sastles-com/FPC-isolation-sphere/blog/tips/ai-conversational-design.md

---
title: "AIと対話しながらハードを設計する —— Claude Codeで球体LEDを作る"
emoji: "🤖"
type: "idea"
topics: ["AI", "ClaudeCode", "設計", "ものづくり", "電子工作"]
published: false
---

> **アウトライン（note=物語 / Zenn idea=両出し）** — 本編リンク元: 00 序章（メタ視点）
> プロセスもの。技術詳細より「どう進めたか」の体験談。最も拡散しうる一本。

## なぜAI対話で設計したのか
- 球体LEDという**幾何 × 回路 × 機構 × ソフト**の横断プロジェクト
- 一人で全領域を抱えるより、AIを設計パートナーにする実験

## ワークフローの実際
- リポジトリに設計知識を集約（`CLAUDE.md` + `docs/NN-*.md`）→ AIが前提を常に把握
- 「確定事項」と「未確定（open questions）」を分けて管理 → AIが勝手に決めない
- スクリプト生成（Goldberg多面体、FPC展開、LED座標CSV）を対話で回す

## うまくいったこと
- 幾何の対称性（5回対称→Gerber1種×10）など、**設計判断の言語化**が進んだ
- ドキュメントが常に最新 → 数ヶ月後の自分が即復帰できる
- 「なぜこの設計か」が対話ログとして残る

## 難しかった・気をつけたこと
- AIが推論で埋めようとする → **「不明点は質問させる」ルール**を明文化
- 確定/未確定の境界管理、ハード規則（NEVER/ALWAYS）の固定
- 最終判断は人間（特に試作検証が要る物理パラメータ）

## この記事自体もAIと書いている
- ブログの章立て・媒体戦略もAIと壁打ちした、というメタなオチ

## 関連
- 本編: 00 序章 / 全シリーズの裏側
