sastles-com/FPC-isolation-sphere/blog/tips/shell-color-black-or-white.md

---
title: "外殻は白か黒か？ —— 球体LEDディスプレイの外装色を決める"
emoji: "⚫"
type: "tech"
topics: ["3Dプリンタ", "電子工作", "LED", "設計", "光学"]
published: false
---

> **アウトライン（Zenn Scrap向き：結論が固まったらArticle化）** — 本編リンク元: 01 シェル設計
> 設計docsの方針: 黒（反射抑制のブラックマスク効果）。本記事はそのトレードオフを言語化する。

## 何を悩んでいるか
- 外装色は見た目だけでなく**光学性能**を左右する設計パラメータ
- 候補: 黒 / 白 / その他（グレー・スモーク等）

## 黒のメリット
- ラッパ穴周囲が**遮光マスク**になり、隣接LEDの光の滲みを抑え**コントラスト向上**
- 消灯時に「黒い球」として締まる、映像の黒が沈む
- 反射抑制 → 球面の映像が読みやすい

## 白のメリット（と却下理由）
- 拡散して柔らかい印象 / 消灯時の存在感
- ただし**滲み・コントラスト低下** → 映像ディスプレイとしては不利

## ラッパ穴構造との相互作用
- 黒 + 円錐ラッパ穴 = 二重のブラックマスク（記事01と接続）
- PETG黒の表面処理（マット/グロス）で反射がどう変わるか

## 決定と根拠
- **黒を採用**（ディスプレイとしてのコントラスト最優先）
- 試作で詰める点: マット/グロス、艶消し塗装の要否、内面反射の実測

## 関連
- 本編: 01 シェル設計（ラッパ穴の光学設計）
