sastles-com/FPC-isolation-sphere/docs/各図.pptx

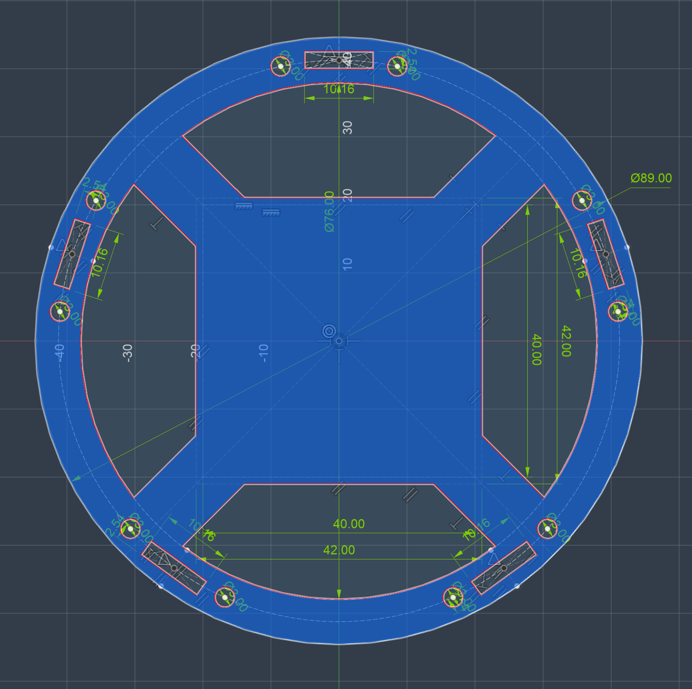
[picture p6: figure]

マザーリング

ポゴピン

電池・基板スペース

## Slide 2

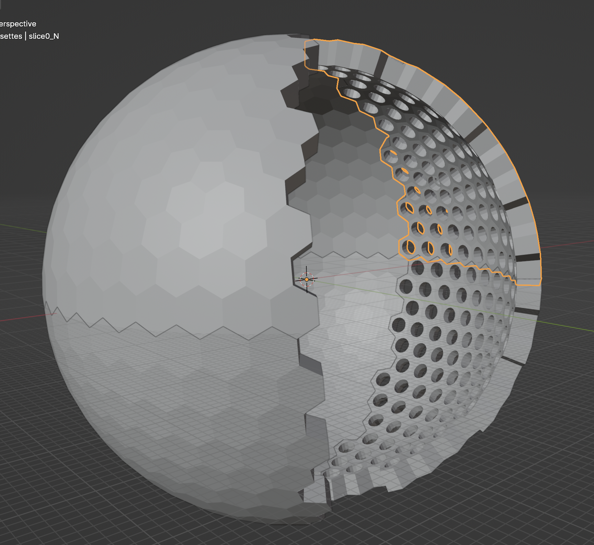
[picture p7: figure]

## Slide 3
