sastles-com/FPC-isolation-sphere/blog/images/28dac7f0-c07c-42df-aeb3-657aa2e844b5.jpeg

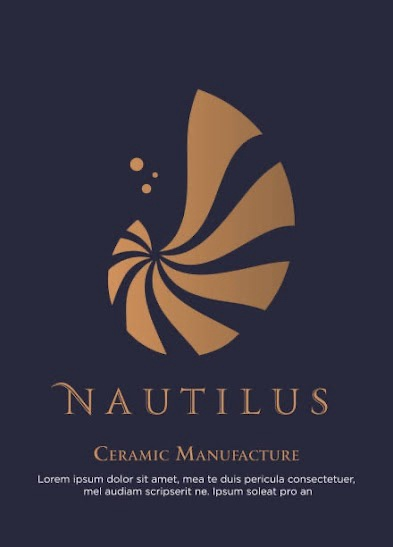
blog/images/28dac7f0-c07c-42df-aeb3-657aa2e844b5.jpeg
