sastles-com/FPC-isolation-sphere/blog/images/2025/IMG_6954.PNG

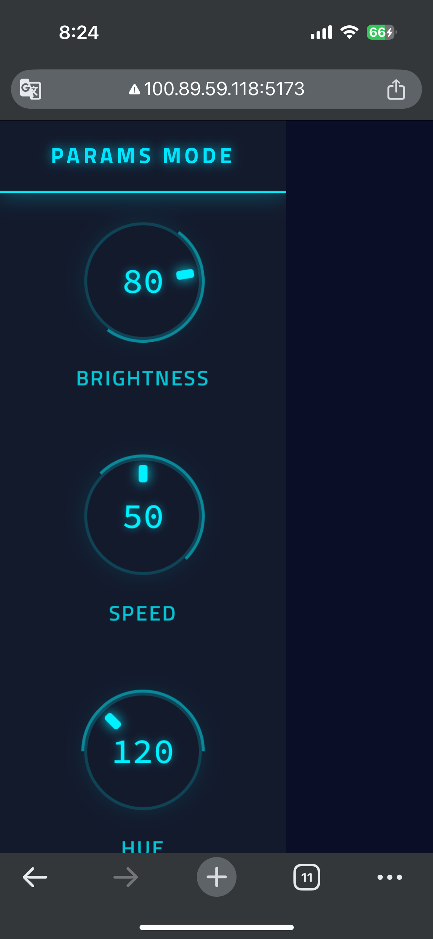
blog/images/2025/IMG_6954.PNG
