sastles-com/FPC-isolation-sphere/blog/images/2025/IMG_6956.PNG

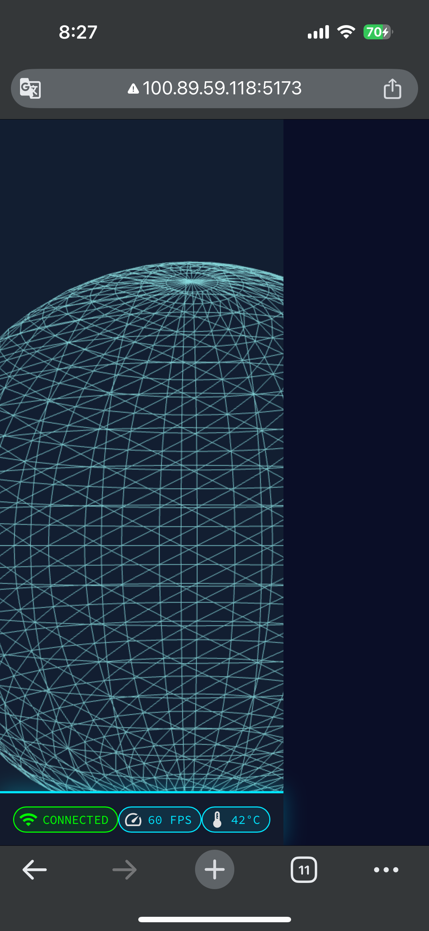
blog/images/2025/IMG_6956.PNG
