sastles-com/FPC-isolation-sphere/blog/images/2025/IMG_7172.PNG

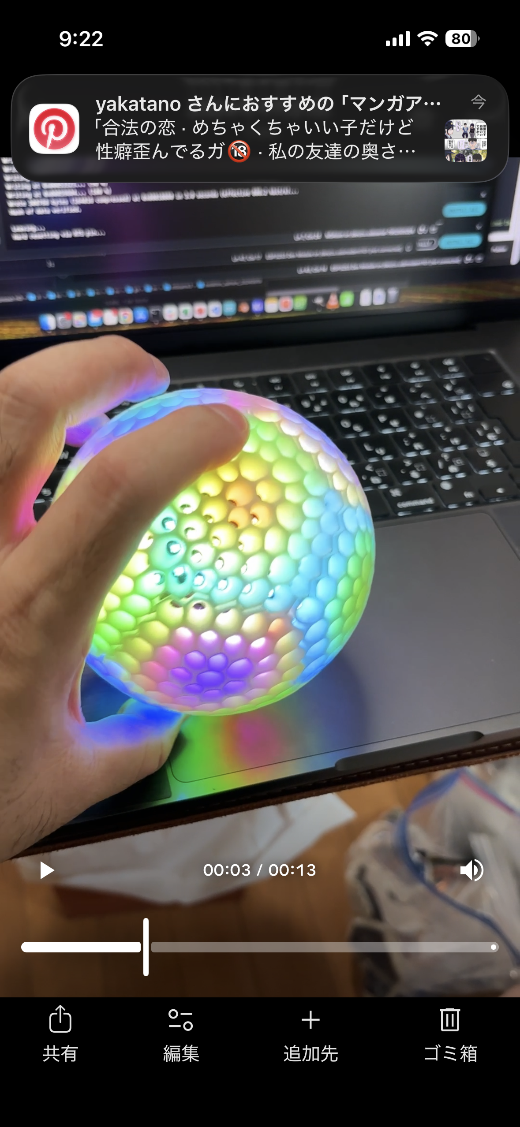
blog/images/2025/IMG_7172.PNG
