sastles-com/FPC-isolation-sphere/blog/images/2025/IMG_7173.PNG

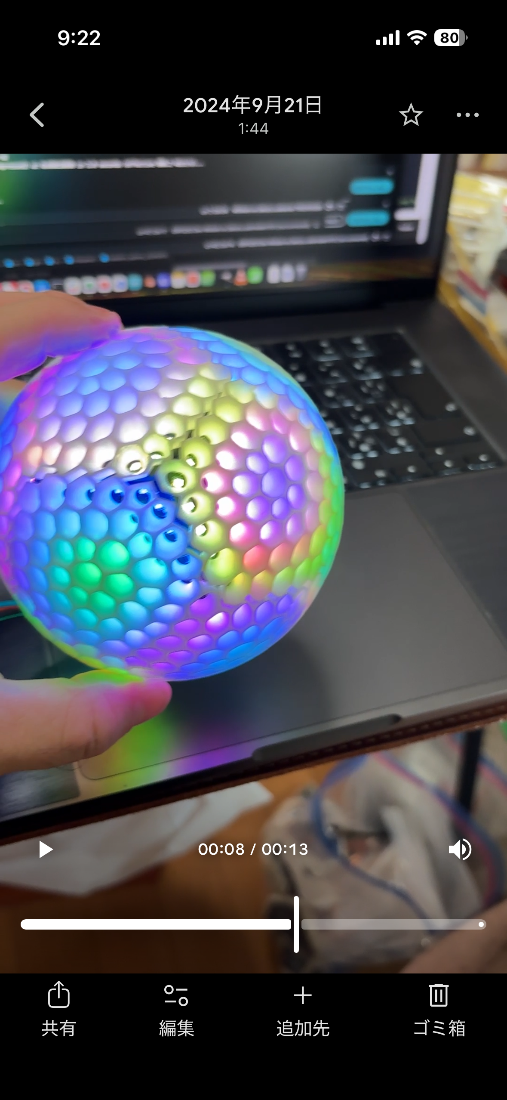
blog/images/2025/IMG_7173.PNG
