sastles-com/FPC-isolation-sphere/blog/images/avocado/IMG_8150.JPG

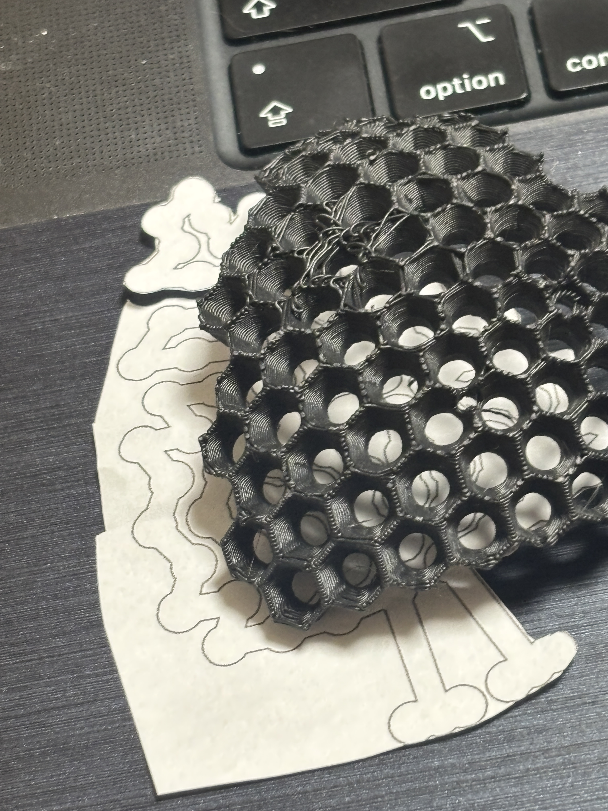
blog/images/avocado/IMG_8150.JPG
