sastles-com/FPC-isolation-sphere/blog/images/avocado/IMG_8152.JPG

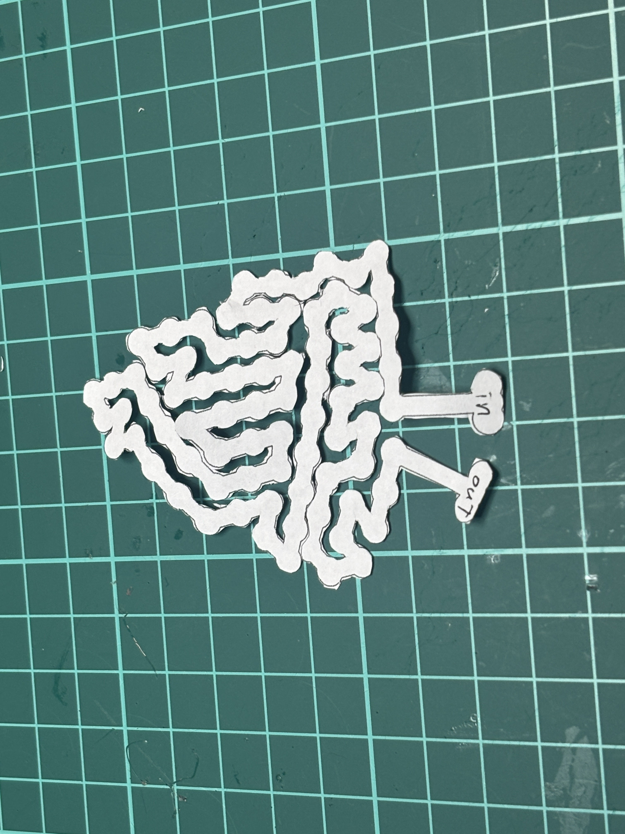
blog/images/avocado/IMG_8152.JPG
