sastles-com/FPC-isolation-sphere/blog/images/avocado/IMG_8159.JPG

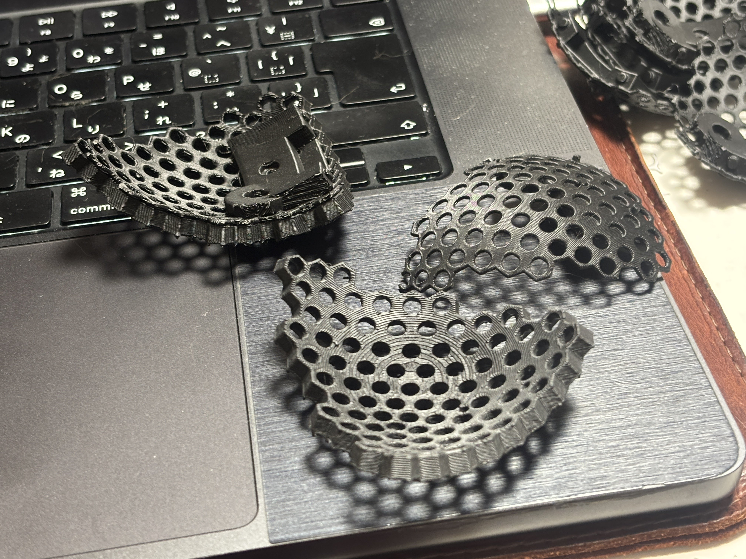
blog/images/avocado/IMG_8159.JPG
