sastles-com/FPC-isolation-sphere/blog/images/avocado/IMG_8160.JPG

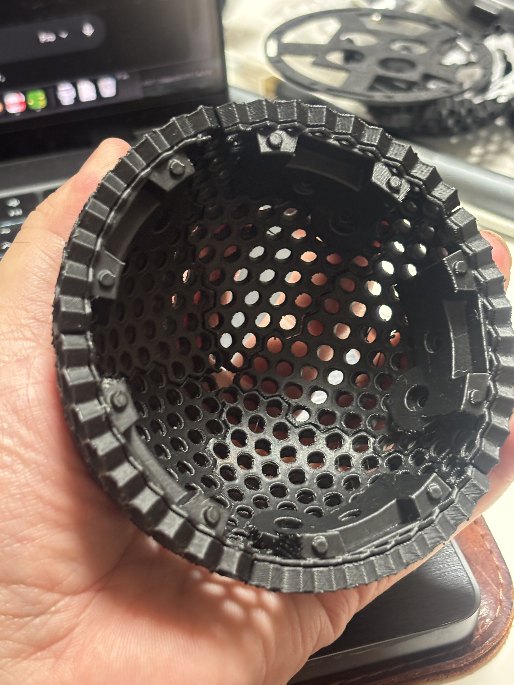
blog/images/avocado/IMG_8160.JPG
