sastles-com/FPC-isolation-sphere/blog/images/avocado/IMG_8166.JPG

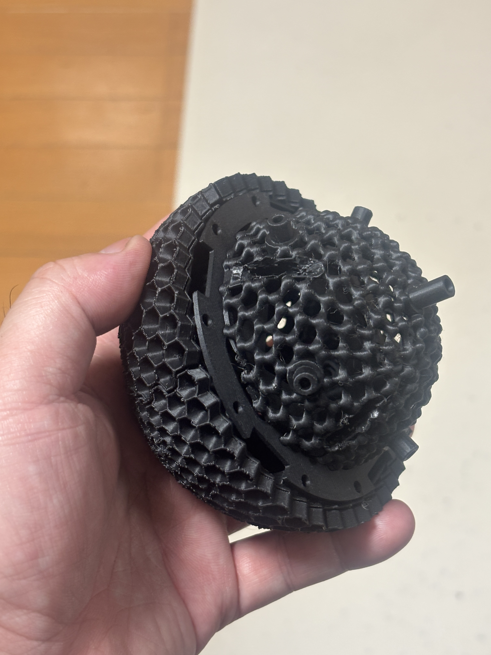
blog/images/avocado/IMG_8166.JPG
