sastles-com/FPC-isolation-sphere/blog/images/avocado/IMG_8167.JPG

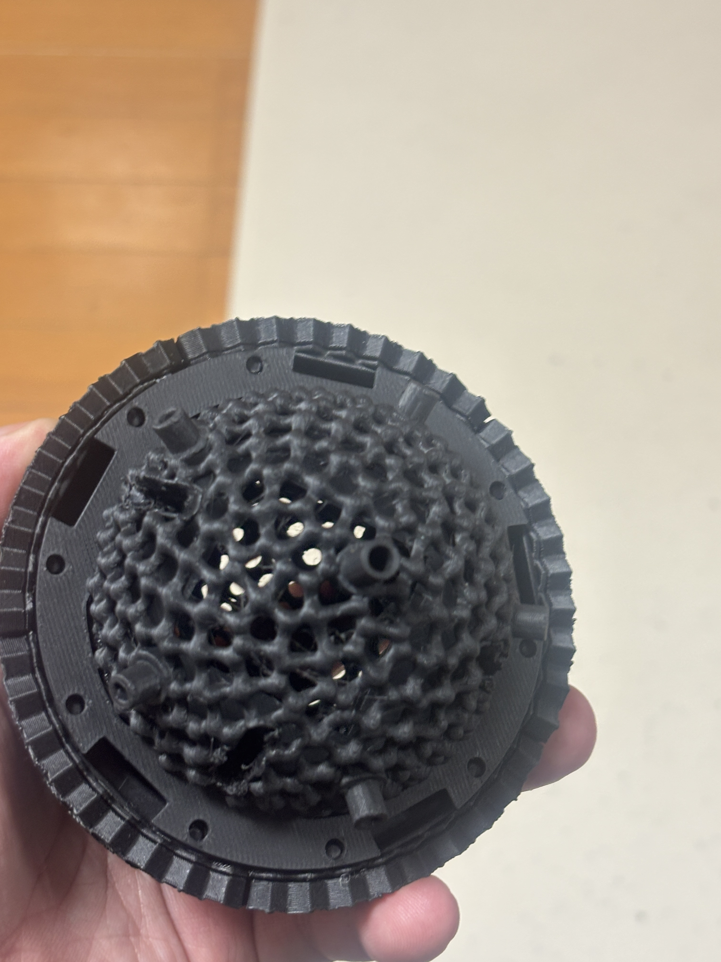
blog/images/avocado/IMG_8167.JPG
