sastles-com/FPC-isolation-sphere/blog/images/avocado/IMG_8190.JPG

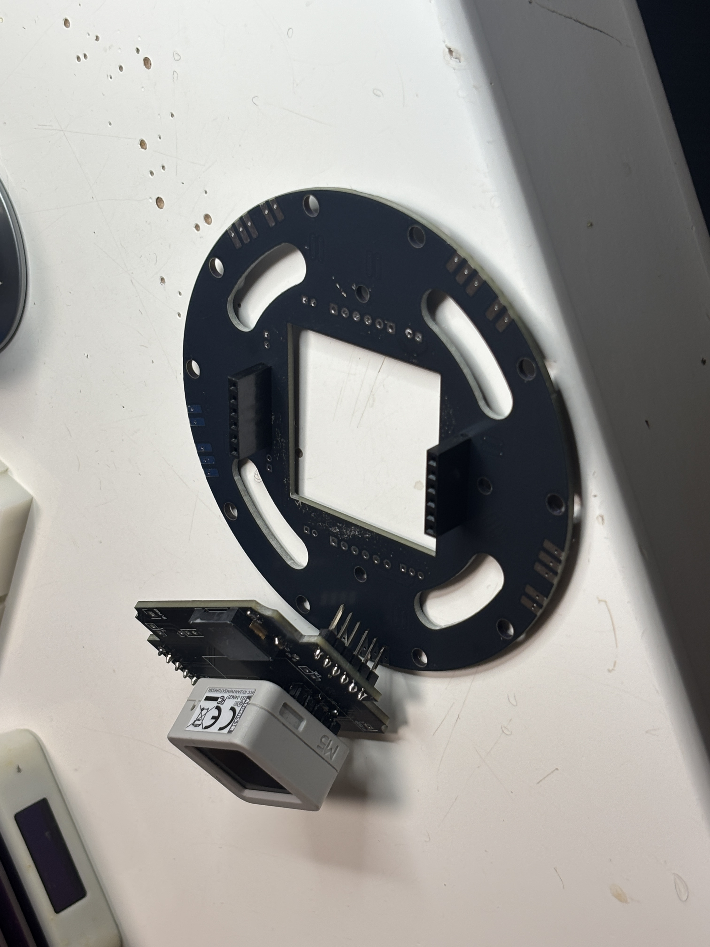
blog/images/avocado/IMG_8190.JPG
