sastles-com/FPC-isolation-sphere/blog/images/avocado/IMG_8191.JPG

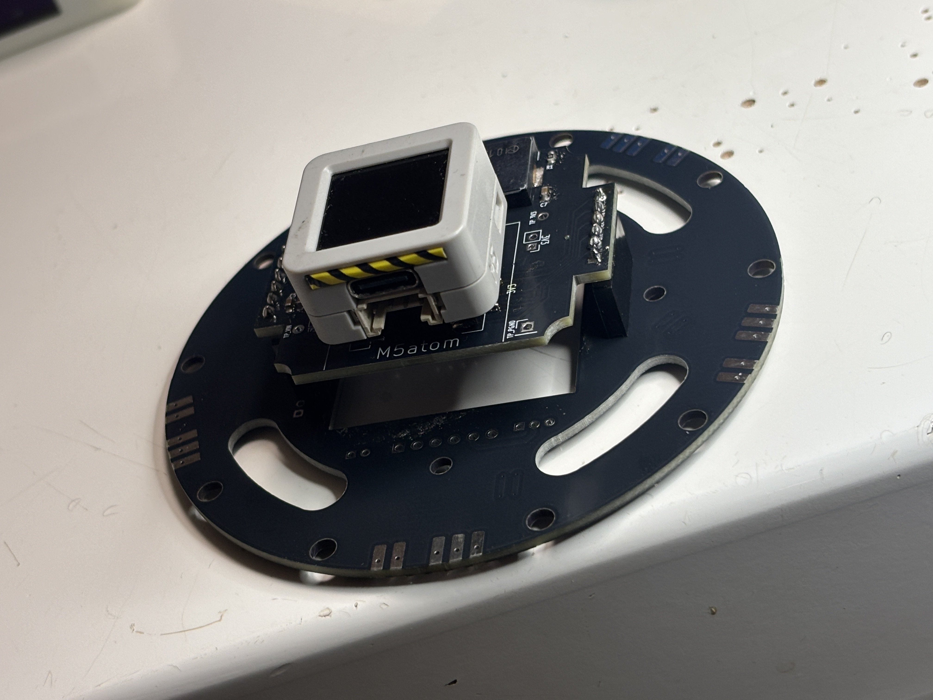
blog/images/avocado/IMG_8191.JPG
