sastles-com/FPC-isolation-sphere/blog/images/avocado/IMG_8192.JPG

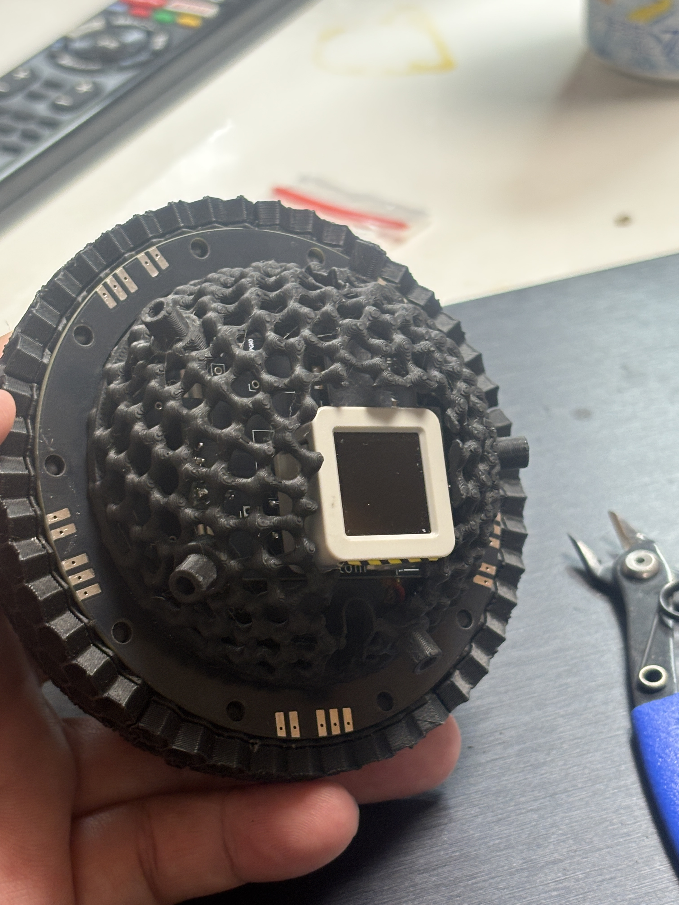
blog/images/avocado/IMG_8192.JPG
