sastles-com/FPC-isolation-sphere/blog/images/avocado/IMG_8193.JPG

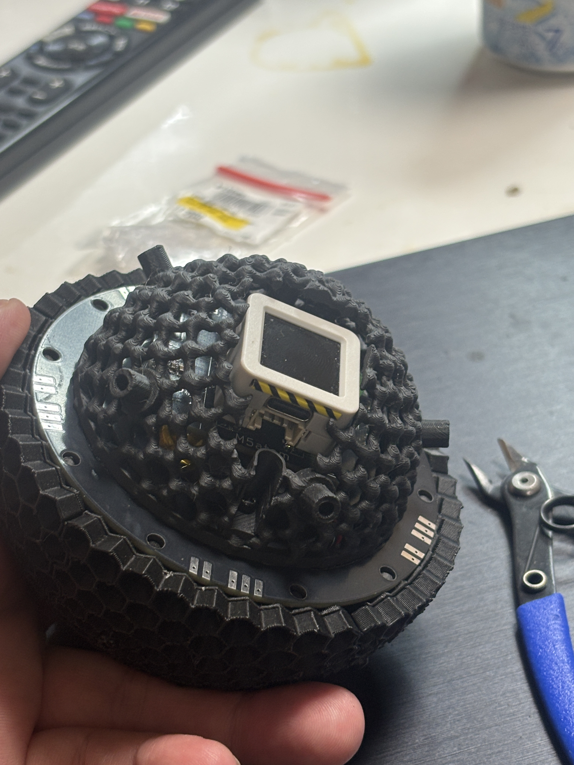
blog/images/avocado/IMG_8193.JPG
