sastles-com/FPC-isolation-sphere/blog/images/avocado/IMG_8194.JPG

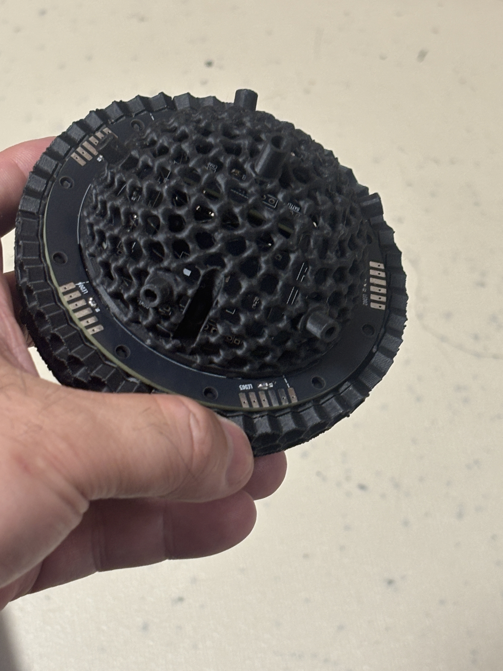
blog/images/avocado/IMG_8194.JPG
