sastles-com/FPC-isolation-sphere/blog/images/avocado/IMG_8195.JPG

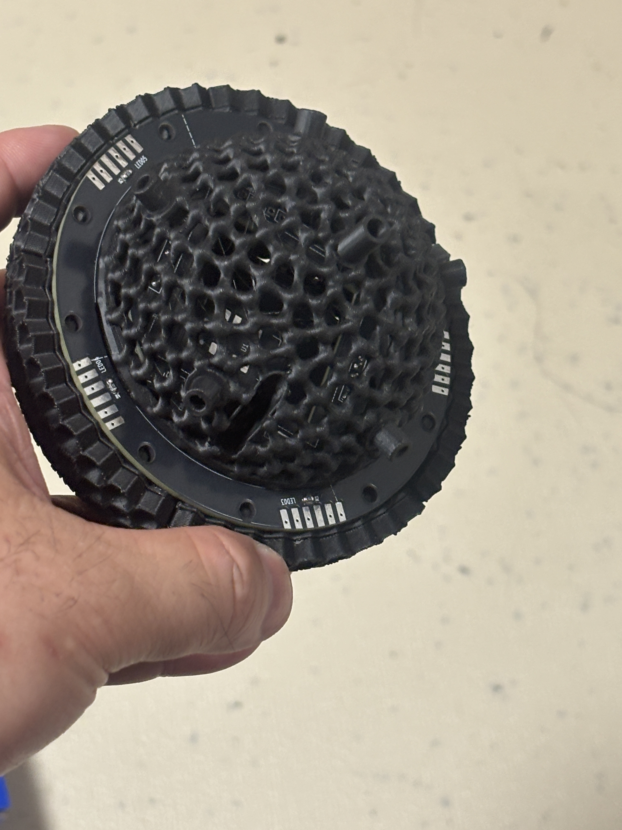
blog/images/avocado/IMG_8195.JPG
