sastles-com/FPC-isolation-sphere/blog/images/avocado/IMG_8196.JPG

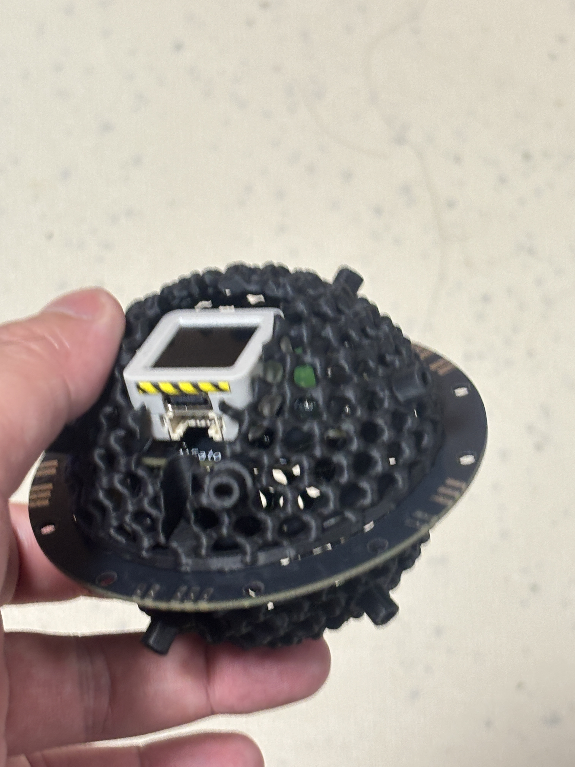
blog/images/avocado/IMG_8196.JPG
