sastles-com/FPC-isolation-sphere/blog/images/avocado/IMG_8197.JPG

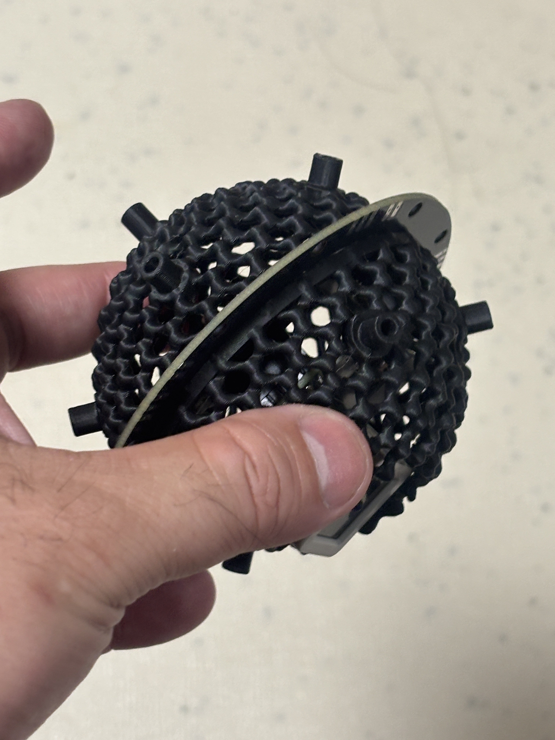
blog/images/avocado/IMG_8197.JPG
