sastles-com/FPC-isolation-sphere/blog/images/avocado/IMG_8198.JPG

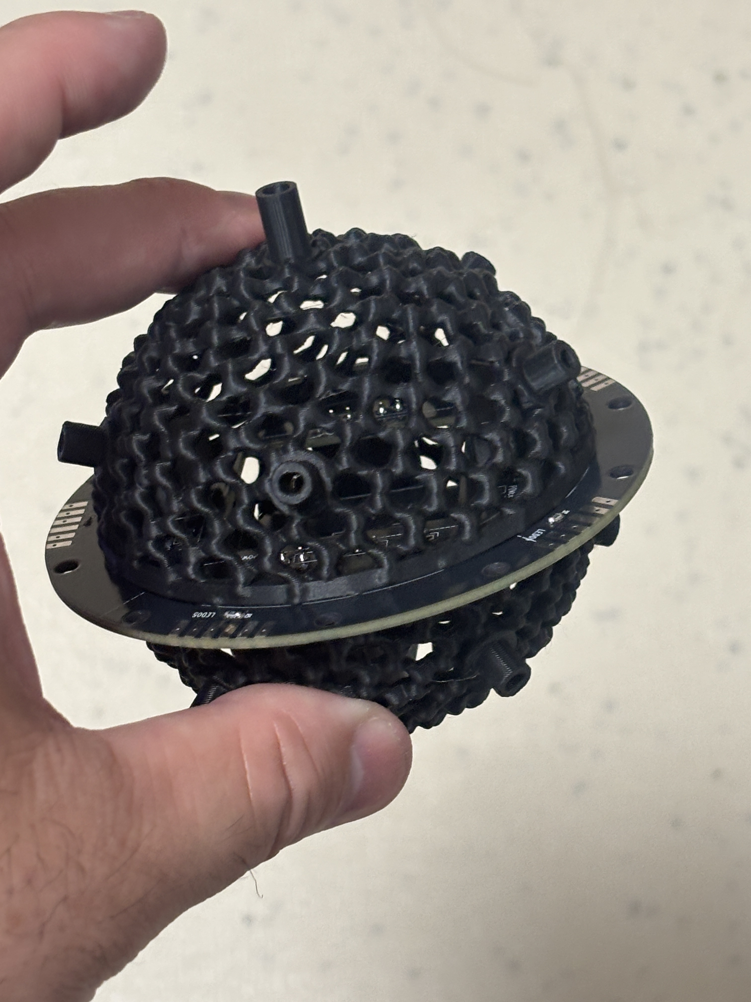
blog/images/avocado/IMG_8198.JPG
