sastles-com/FPC-isolation-sphere/blog/images/dodecahedron/IMG_7805.JPG

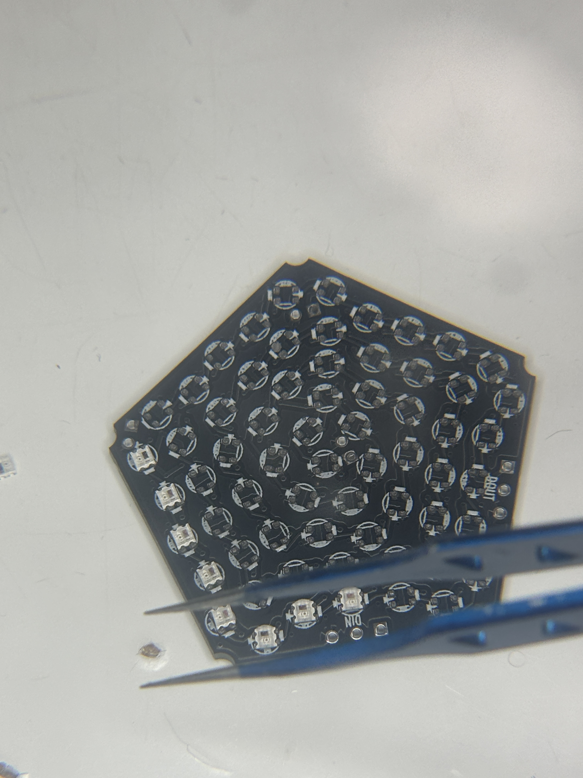
blog/images/dodecahedron/IMG_7805.JPG
