sastles-com/FPC-isolation-sphere/blog/images/dodecahedron/IMG_7879.JPG

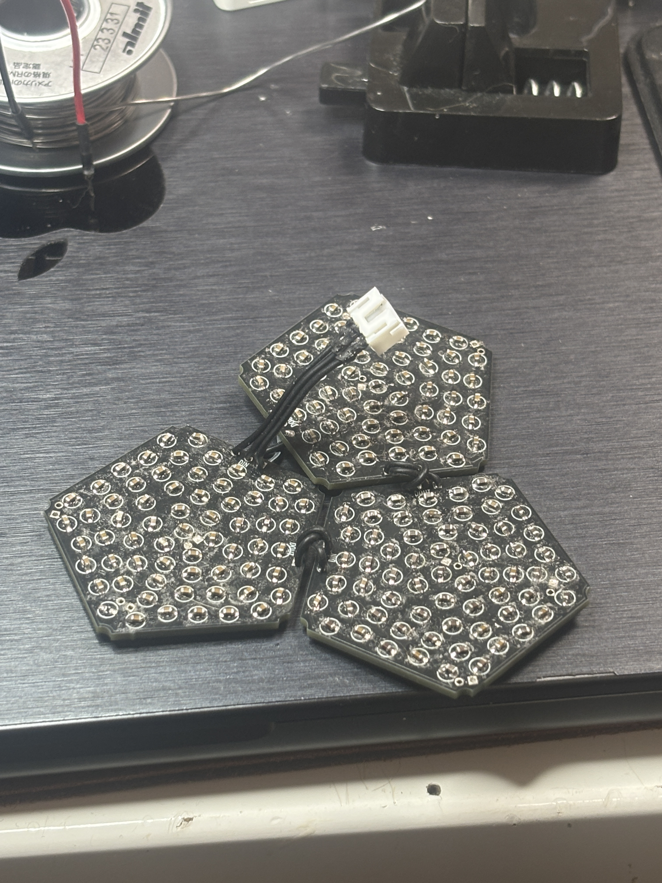
blog/images/dodecahedron/IMG_7879.JPG
