sastles-com/FPC-isolation-sphere/blog/images/dodecahedron/IMG_7970.PNG

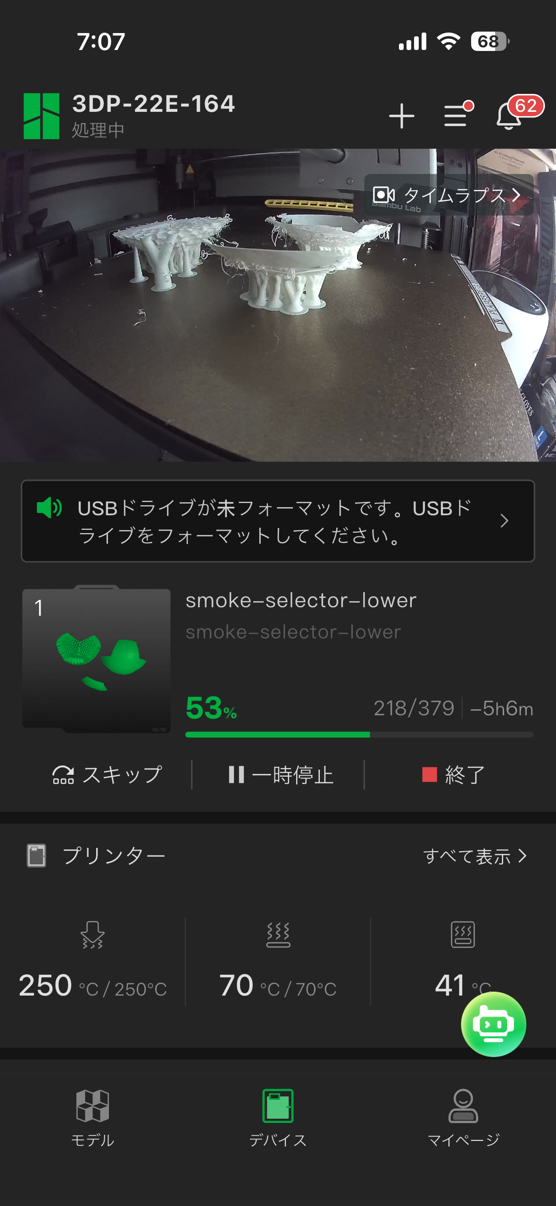
blog/images/dodecahedron/IMG_7970.PNG
