sastles-com/FPC-isolation-sphere/blog/images/dodecahedron/IMG_7981.JPG

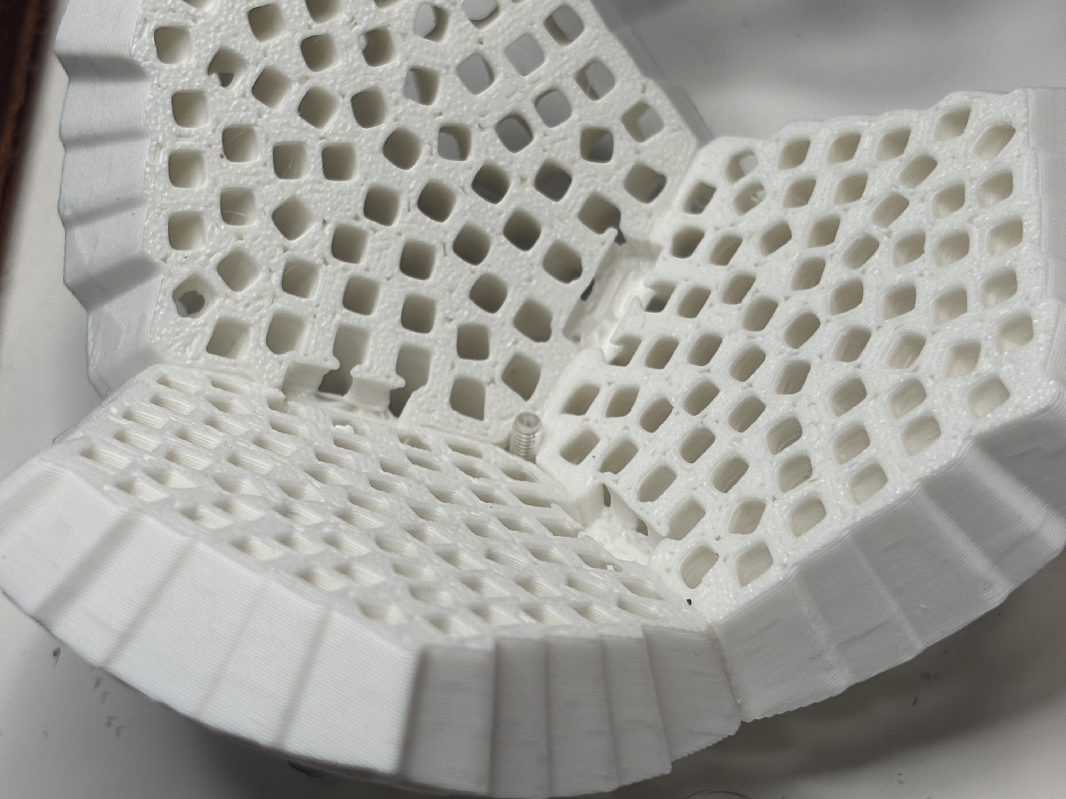
blog/images/dodecahedron/IMG_7981.JPG
