sastles-com/FPC-isolation-sphere/blog/images/dodecahedron/IMG_8008.JPG

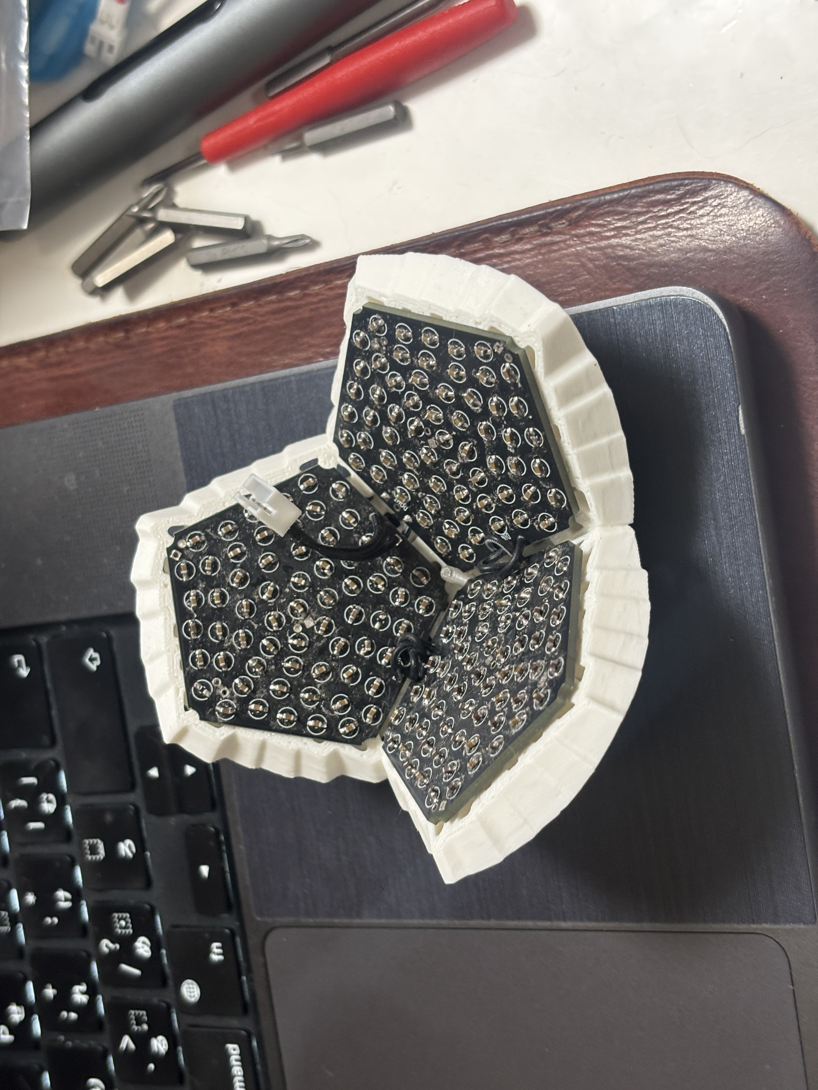
blog/images/dodecahedron/IMG_8008.JPG
