sastles-com/FPC-isolation-sphere/blog/images/dodecahedron/IMG_8009.JPG

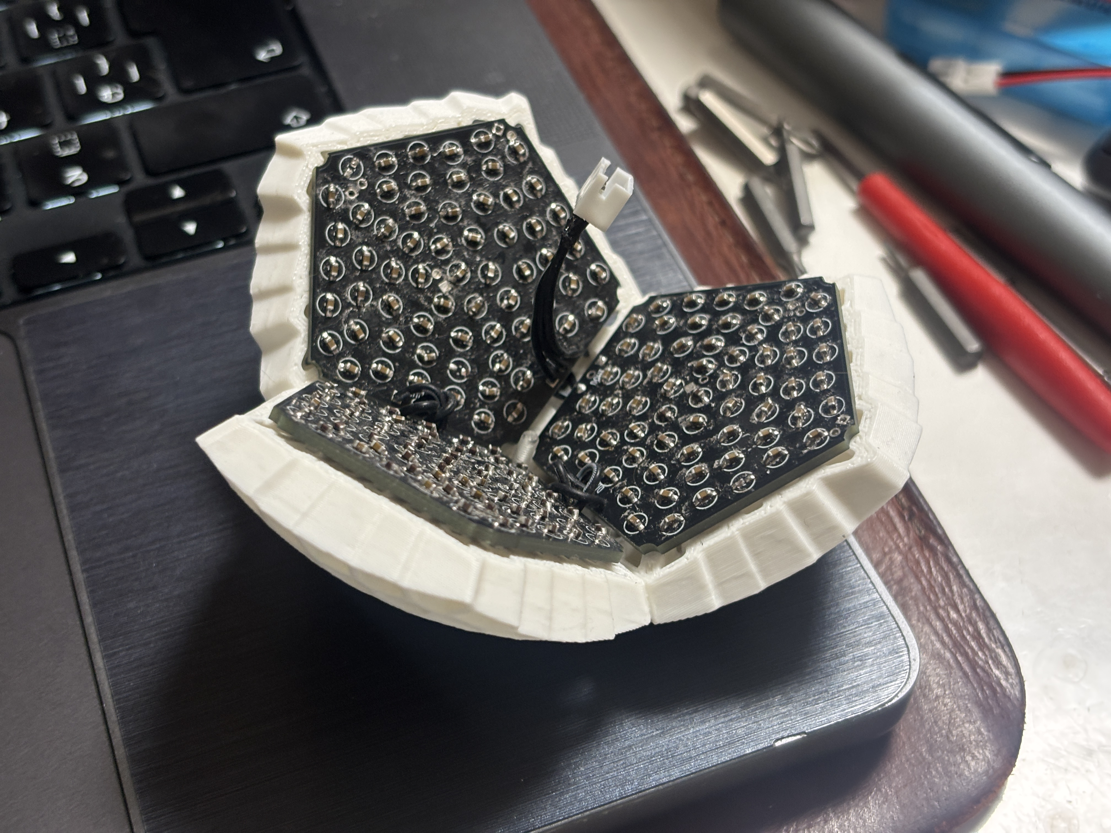
blog/images/dodecahedron/IMG_8009.JPG
