sastles-com/FPC-isolation-sphere/blog/images/dodecahedron/IMG_8010.JPG

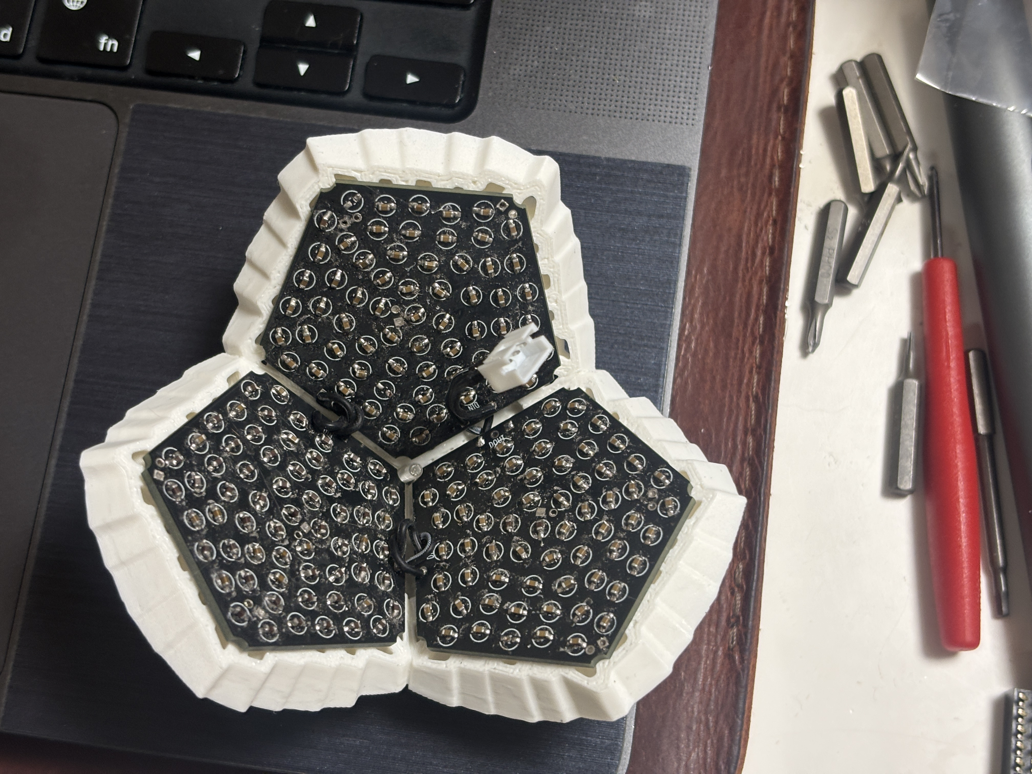
blog/images/dodecahedron/IMG_8010.JPG
