sastles-com/FPC-isolation-sphere/blog/images/dodecahedron/IMG_8016.JPG

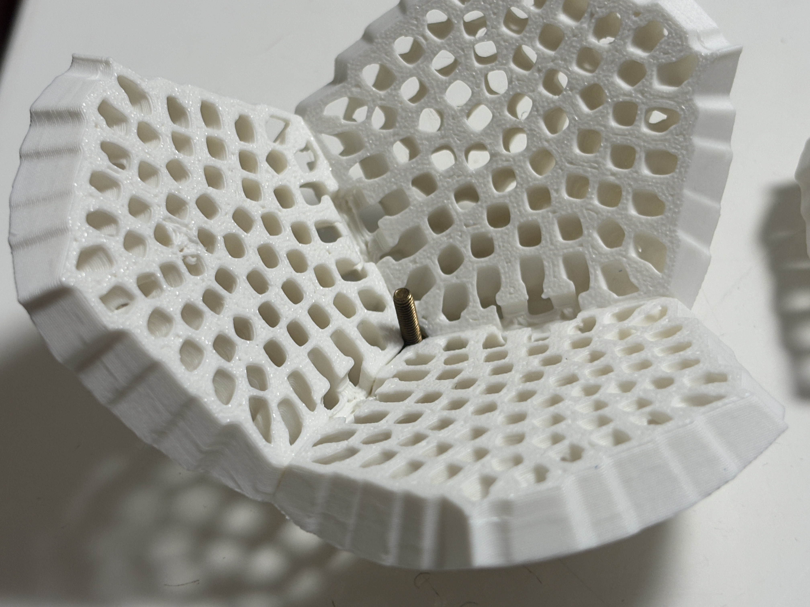
blog/images/dodecahedron/IMG_8016.JPG
