sastles-com/FPC-isolation-sphere/blog/images/dodecahedron/IMG_8122.JPG

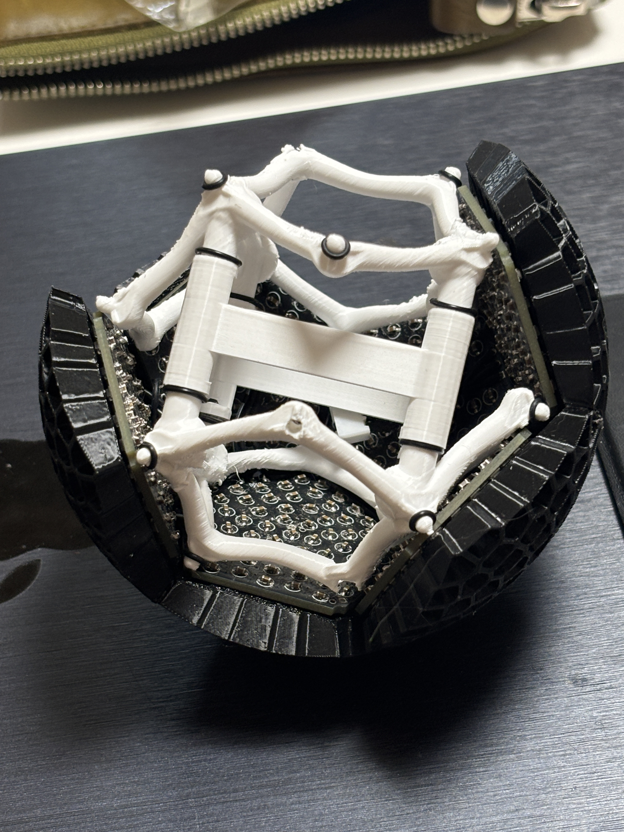
blog/images/dodecahedron/IMG_8122.JPG
