sastles-com/FPC-isolation-sphere/blog/images/nautilus.jpeg

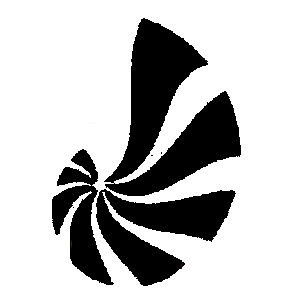
blog/images/nautilus.jpeg
