sastles-com/FPC-isolation-sphere/docs/images/fpc_kicad_halfgore--.png

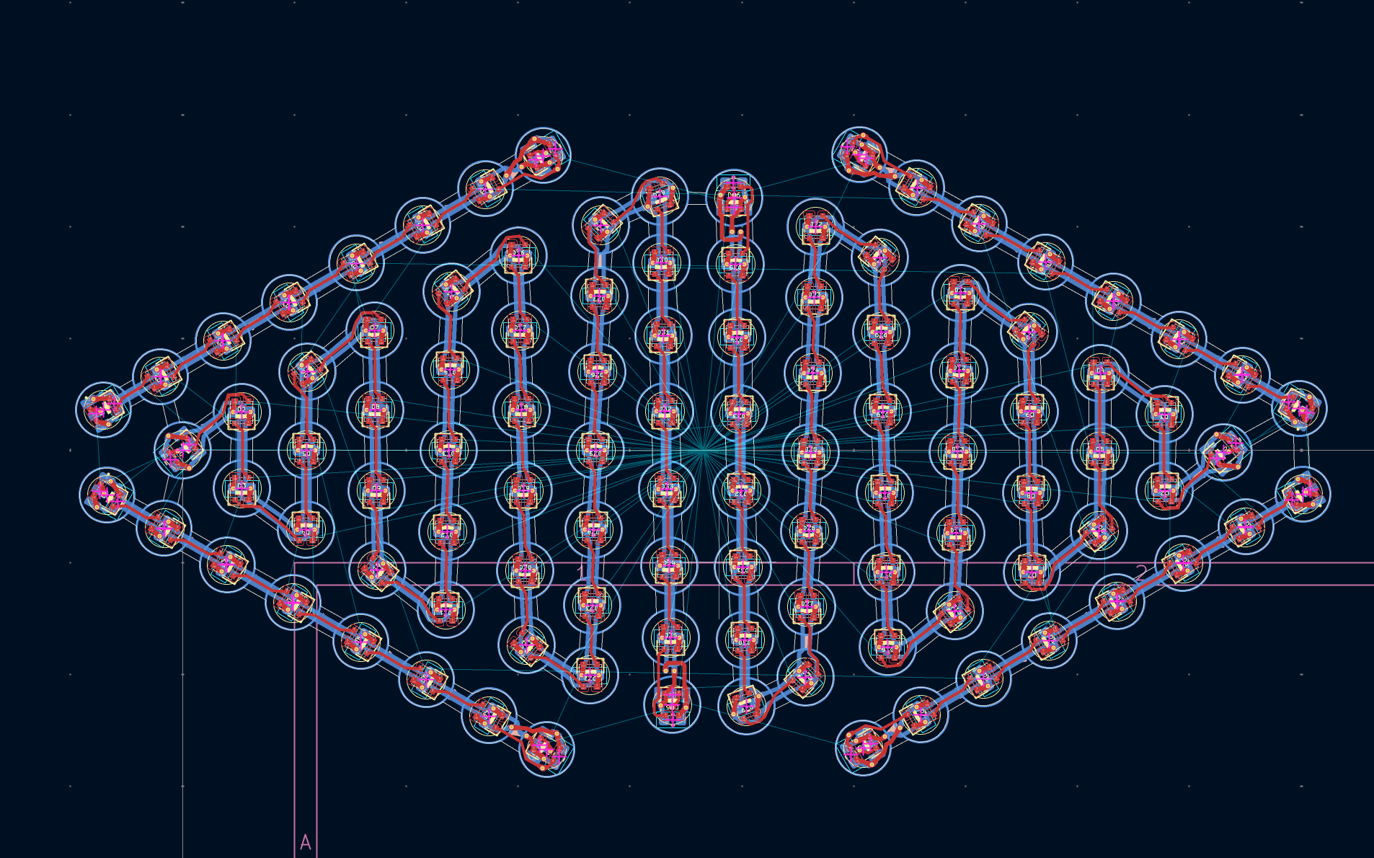
docs/images/fpc_kicad_halfgore--.png
