sastles-com/FPC-isolation-sphere/kiban/power-IP2326-MP1584/jlcpcb/production_files/BOM-power_IP2326_MP1584.csv

Comment | Designator | Footprint | LCSC | Quantity
10kΩ | R2 | R_0603_1608Metric |  | 1
10kΩ | R1 | R_0603_1608Metric |  | 1
BATTERY | J3 | PinHeader_1x02_P2.00mm_Vertical |  | 1
22uF | C5 | C_0805_2012Metric |  | 1
0.1uF | C4 | C_0603_1608Metric |  | 1
TP2326 | U2 | TS2326 |  | 1
CHARGE | J14 | PinHeader_1x02_P2.00mm_Vertical |  | 1
BATTERY | J2 | PinHeader_1x03_P2.00mm_Vertical |  | 1
22uF | C3 | C_0805_2012Metric |  | 1
100uF | C1 | CP_EIA-3528-12_Kemet-T |  | 1
100uF | C7 | CP_EIA-3528-12_Kemet-T |  | 1
EN | J8 | PinHeader_1x01_P2.54mm_TP |  | 1
22uF | C6 | C_0805_2012Metric |  | 1
OUTPUT | J4 | PinHeader_1x02_P2.00mm_Vertical |  | 1
FerriteBead | FB1 | L_0603_1608Metric |  | 1
MMBT3904 | Q1 | SOT-23 |  | 1
MP1584EN | U3 | MP1584EN |  | 1
0.1uF | C2 | C_0603_1608Metric |  | 1
10kΩ | R3 | R_0603_1608Metric |  | 1
OUTPUT | J9 | PinHeader_1x02_P2.00mm_Vertical |  | 1
REMOTE | J7 | PinHeader_1x04_P2.00mm_Vertical |  | 1
