sastles-com/FPC-isolation-sphere/kiban/power-IP2326-MP1584/power-IP2326-MP1584.kicad_pcb

## KiCad design kiban/power-IP2326-MP1584/power-IP2326-MP1584.kicad_pcb (2026-07-06)

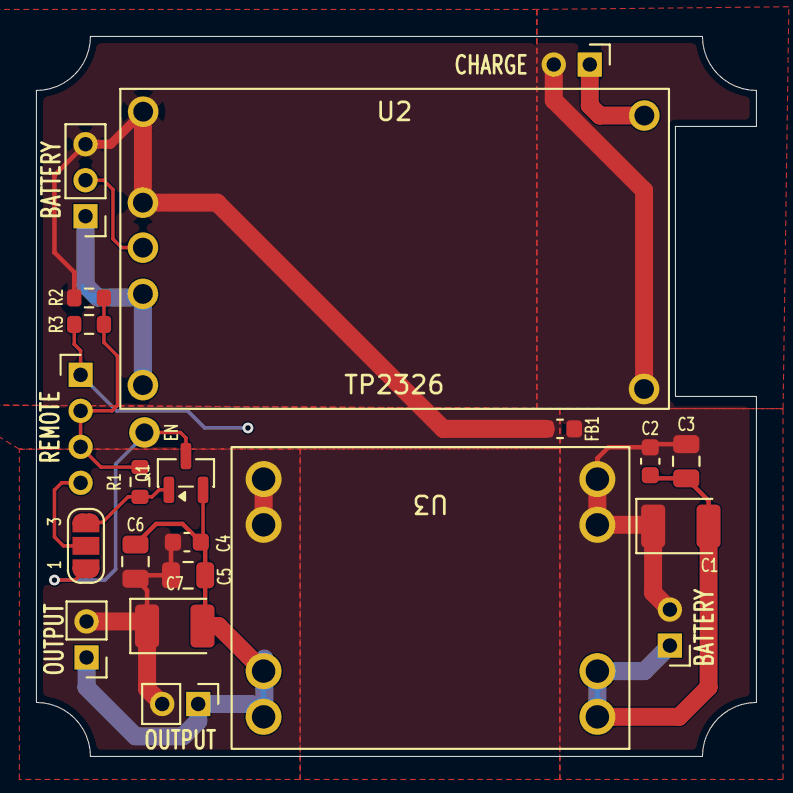
[picture p117: board power-IP2326-MP1584.kicad_pcb from above]

Board: 2 copper layers, 40.0 x 40.0 mm, 22 parts (0 on the bottom side), 11 nets.

Parts:
C1, C7: 100uF; CP_EIA-3528-12_Kemet-T
C2, C4: 0.1uF; C_0603_1608Metric
C3, C5, C6: 22uF; C_0805_2012Metric
FB1: FerriteBead; L_0603_1608Metric
J2: BATTERY; PinHeader_1x03_P2.00mm_Vertical
J3: BATTERY; PinHeader_1x02_P2.00mm_Vertical
J4, J9: OUTPUT; PinHeader_1x02_P2.00mm_Vertical
J7: REMOTE; PinHeader_1x04_P2.00mm_Vertical
J8: EN; PinHeader_1x01_P2.54mm_TP
J14: CHARGE; PinHeader_1x02_P2.00mm_Vertical
JP1: JUMP; SolderJumper-3_P1.3mm_Open_RoundedPad1.0x1.5mm_NumberLabels
Q1: MMBT3904; SOT-23
R1, R2, R3: 10kΩ; R_0603_1608Metric
U2: TP2326; TS2326
U3: MP1584EN

Connections:
BM: J2.2, U2.2 (BM)
EN: J8.1 (Pin_1_1), JP1.1 (A), Q1.3 (C)
unnamed: JP1.3 (B), Q1.1 (B), R1.1
P+: FB1.1, J2.3, R2.2, U2.1 (B+)
P-: J2.1, U2.3 (B-)
PGND: C1.2, C2.2, C3.2, C4.2, C5.2, C6.2, C7.2, J3.1, J4.1, J7.1, J9.1, J14.1, Q1.2 (E), R3.2, U2.5 (GND), U3.1 (IN-), U3.4 (OUT-)
POUT: J14.2, U2.4 (VIN)
SWITCH: J7.4, JP1.2 (C)
VCC: J7.2, J7.3, R1.2, R2.1, R3.1
VIN: C1.1, C2.1, C3.1, FB1.2, J3.2, U3.2 (IN+)
VOUT: C4.1, C5.1, C6.1, C7.1, J4.2, J9.2, U3.3 (OUT+)
