sastles-com/FPC-isolation-sphere/kiban/core-XIAO-03/core-XIAOのコピー.kicad_pcb

## KiCad design kiban/core-XIAO-03/core-XIAOのコピー.kicad_pcb (2026-07-06)

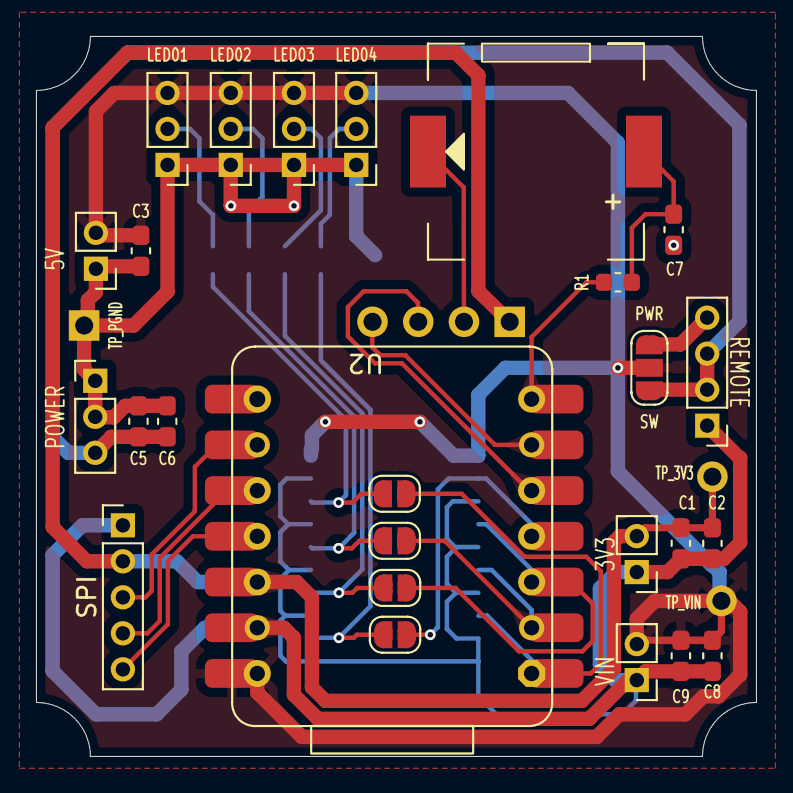
[picture p118: board core-XIAOのコピー.kicad_pcb from above]

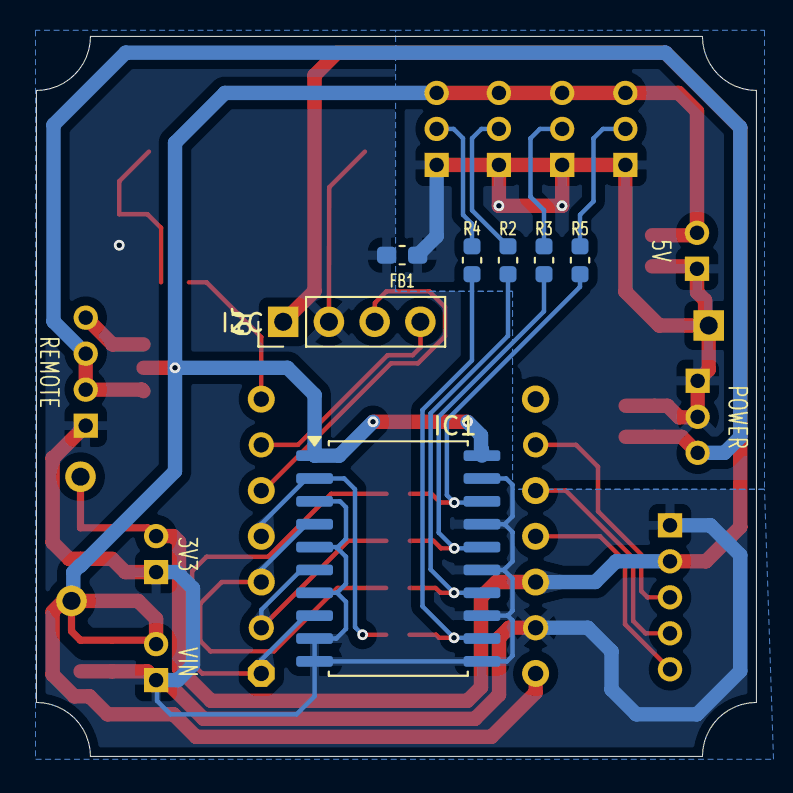
[picture p119: board core-XIAOのコピー.kicad_pcb from below]

Board: 2 copper layers, 40.0 x 40.0 mm, 36 parts (7 on the bottom side), 25 nets.

Parts:
C1, C5, C8: 10uF; C_0603_1608Metric_Pad1.08x0.95mm_HandSolder
C2, C3, C6, C7, C9: 0.1uF; C_0603_1608Metric_Pad1.08x0.95mm_HandSolder
FB1: FerriteBead_Small; C_0603_1608Metric_Pad1.08x0.95mm_HandSolder
IC1: 74HCT245; SOIC-20W_7.5x12.8mm_P1.27mm
J1: POWER; PinHeader_1x03_P2.00mm_Vertical
J2: REMOTE; PinHeader_1x04_P2.00mm_Vertical
J3: SPI; PinHeader_1x05_P2.00mm_Vertical
J5: 3V3; PinHeader_1x02_P2.00mm_Vertical
J6: 5V; PinHeader_1x02_P2.00mm_Vertical
J7: LED03; PinHeader_1x03_P2.00mm_Vertical
J8: LED02; PinHeader_1x03_P2.00mm_Vertical
J9: I2C; PinHeader_1x04_P2.54mm_Vertical
J10: LED04; PinHeader_1x03_P2.00mm_Vertical
J11: LED01; PinHeader_1x03_P2.00mm_Vertical
J12: TP_VIN; PinHeader_1x01_P2.54mm_Vertical
J13: TP_3V3; PinHeader_1x01_P2.54mm_Vertical
J14: TP_PGND; PinHeader_1x01_P2.54mm_Vertical
J15: VIN; PinHeader_1x02_P2.00mm_Vertical
JP1: SolderJumper_3_Open; SolderJumper-3_P1.3mm_Open_RoundedPad1.0x1.5mm_NumberLabels
JP2, JP3, JP4, JP5: SolderJumper_2_Open; SolderJumper-2_P1.3mm_Open_RoundedPad1.0x1.5mm
LS1: SPEAKER; speaker-PKLCS1212
R1: 0Ω; C_0603_1608Metric
R2, R3, R4, R5: 33Ω; C_0603_1608Metric
U2: MOUDLE-SEEEDUINO-XIAO-ESP32S3; XIAO-RP2350

Connections:
3V3: C1.1, C2.1, J3.2, J5.2, J9.1, J13.1, U2.12 (3V3)
AGND: C1.2, C2.2, C7.2, C8.2, C9.2, FB1.2, IC1.3 (A2), IC1.5 (A4), IC1.7 (A6), IC1.9 (A8), IC1.10 (GND), IC1.11 (B8), IC1.13 (B6), IC1.15 (B4), IC1.17 (B2), IC1.19 (~OE), J2.1, J3.1, J5.1, J9.2, J15.1, LS1.LEAD-, U2.13 (GND)
GPIO01: IC1.8 (A7), JP2.1 (A), U2.1 (PA02_A0_D0)
GPIO02: IC1.6 (A5), JP3.1 (A), U2.2 (PA4_A1_D1)
GPIO03: IC1.4 (A3), JP4.1 (A), U2.3 (PA10_A2_D2)
GPIO04: IC1.2 (A1), JP5.1 (A), U2.4 (PA11_A3_D3)
GPIO43: R1.1, U2.7 (PB08_A6_TX)
LED01: IC1.18 (B1), JP2.2 (B), R5.2
LED02: IC1.16 (B3), JP3.2 (B), R3.2
LED03: IC1.14 (B5), JP4.2 (B), R2.2
LED04: IC1.12 (B7), JP5.2 (B), R4.2
unnamed: C7.1, LS1.LEAD+, R1.2
unnamed: J2.4, JP1.3 (B)
unnamed: J7.2, R2.1
unnamed: J8.2, R3.1
unnamed: J10.2, R4.1
unnamed: J11.2, R5.1
PGND: C3.2, C5.2, C6.2, FB1.1, J1.1, J1.2, J6.1, J7.1, J8.1, J10.1, J11.1, J14.1
POWER: C5.1, C6.1, J1.3, J2.2, J2.3, JP1.1 (A)
SCL: J9.4, U2.6 (PA9_A5_D5_SCL)
SDA: J9.3, U2.5 (PA8_A4_D4_SDA)
SPI_MISO: J3.4, U2.10 (PA5_A9_D9_MISO)
SPI_MOSI: J3.5, U2.11 (PA6_A10_D10_MOSI)
SPI_SCK: J3.3, U2.9 (PA7_A8_D8_SCK)
VIN: C3.1, C8.1, C9.1, IC1.1 (DIR), IC1.20 (VCC), J6.2, J7.3, J8.3, J10.3, J11.3, J12.1, J15.2, JP1.2 (C), U2.14 (5V)
