sastles-com/FPC-isolation-sphere/blog/images/2025/IMG_6507.JPG

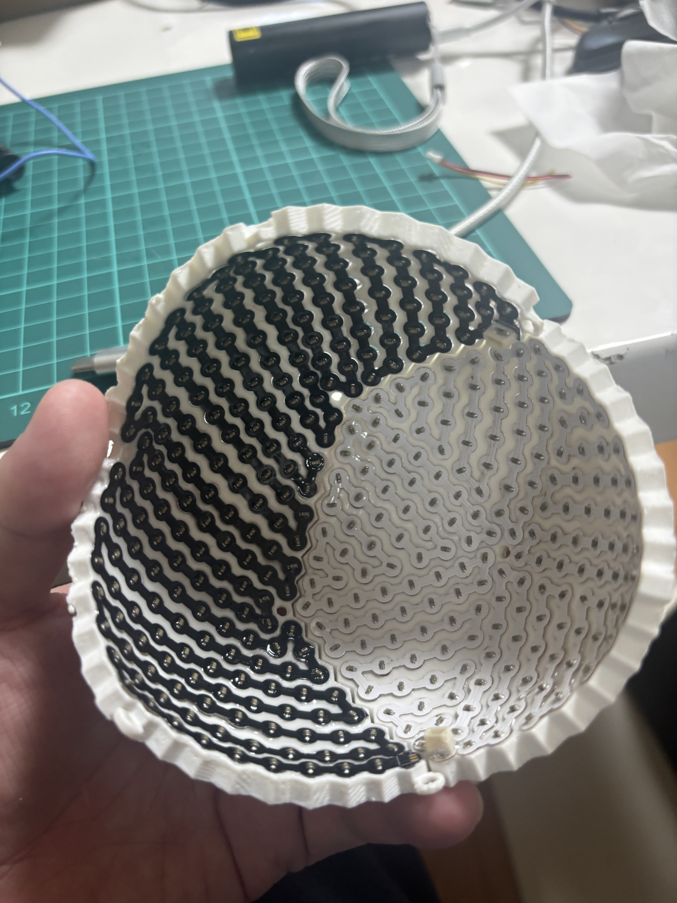
blog/images/2025/IMG_6507.JPG
