sastles-com/FPC-isolation-sphere/blog/images/2025/IMG_6701.JPG

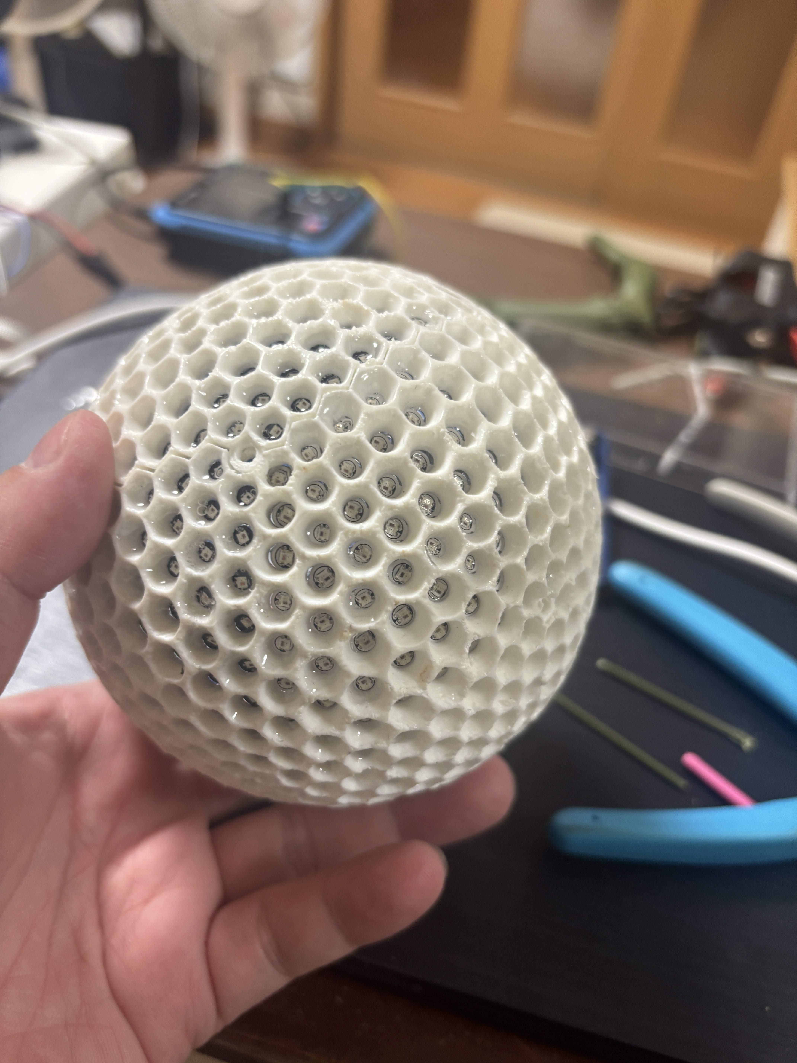
blog/images/2025/IMG_6701.JPG
