sastles-com/FPC-isolation-sphere/blog/images/2025/IMG_7056.JPG

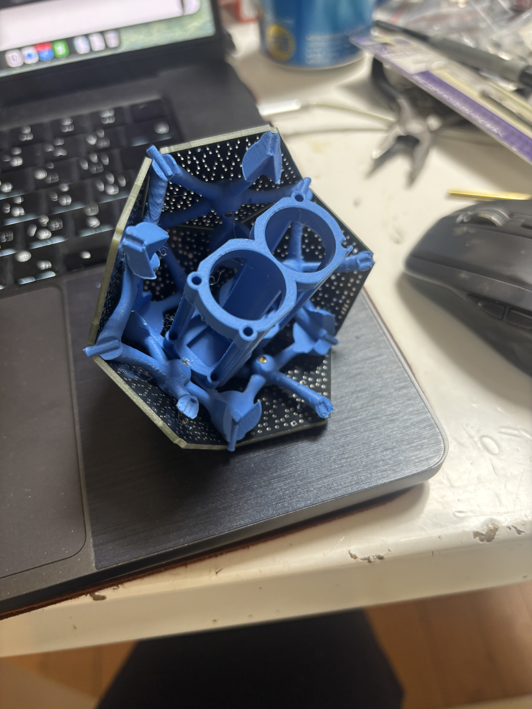
blog/images/2025/IMG_7056.JPG
