sastles-com/FPC-isolation-sphere/blog/images/2025/IMG_7057.JPG

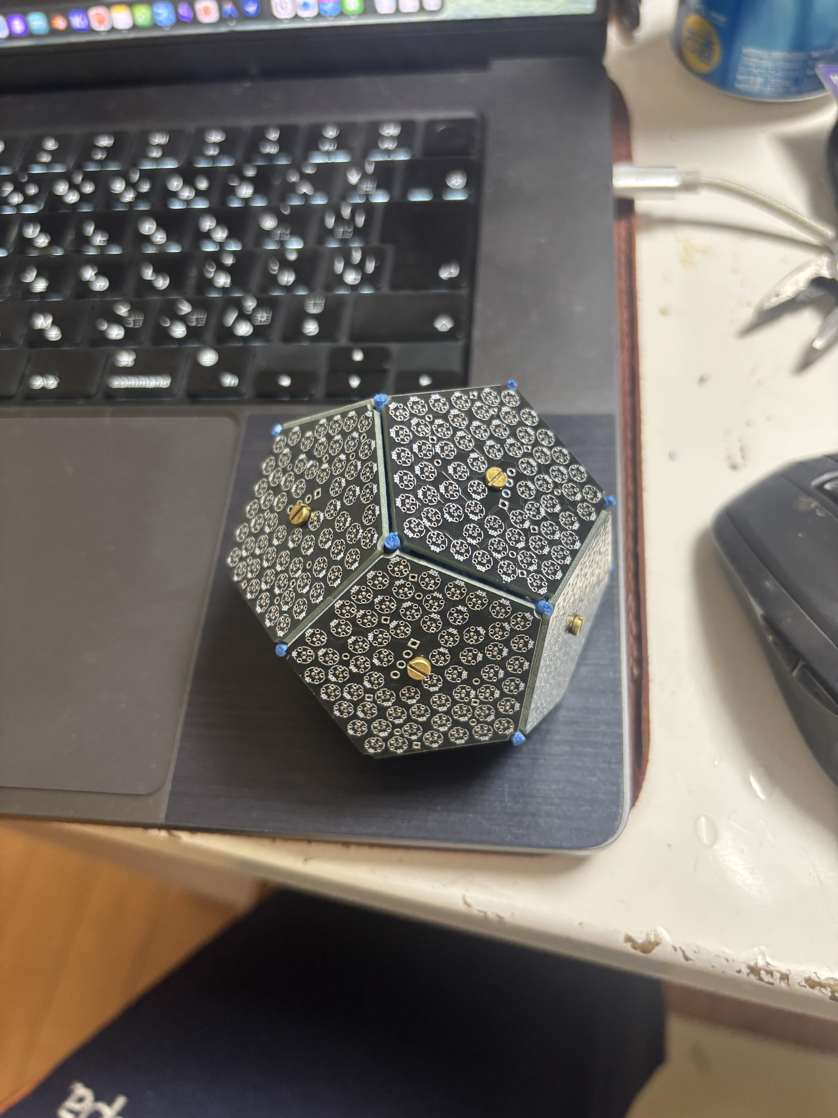
blog/images/2025/IMG_7057.JPG
