sastles-com/FPC-isolation-sphere/blog/images/2025/IMG_7059.JPG

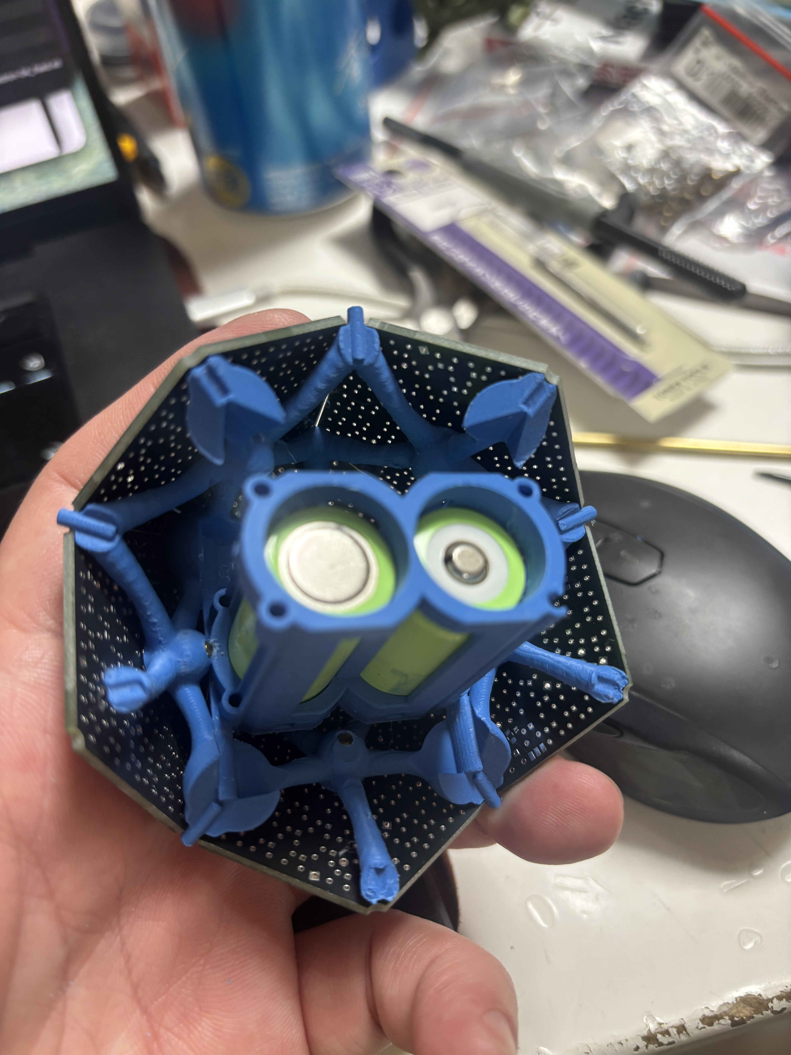
blog/images/2025/IMG_7059.JPG
