sastles-com/FPC-isolation-sphere/blog/images/avocado/IMG_8149.JPG

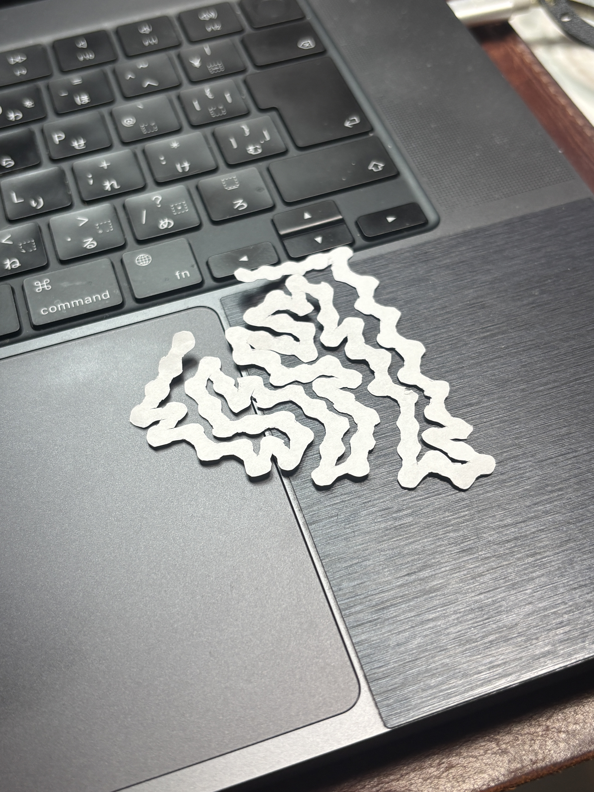
blog/images/avocado/IMG_8149.JPG
