sastles-com/FPC-isolation-sphere/blog/images/avocado/IMG_8151.JPG

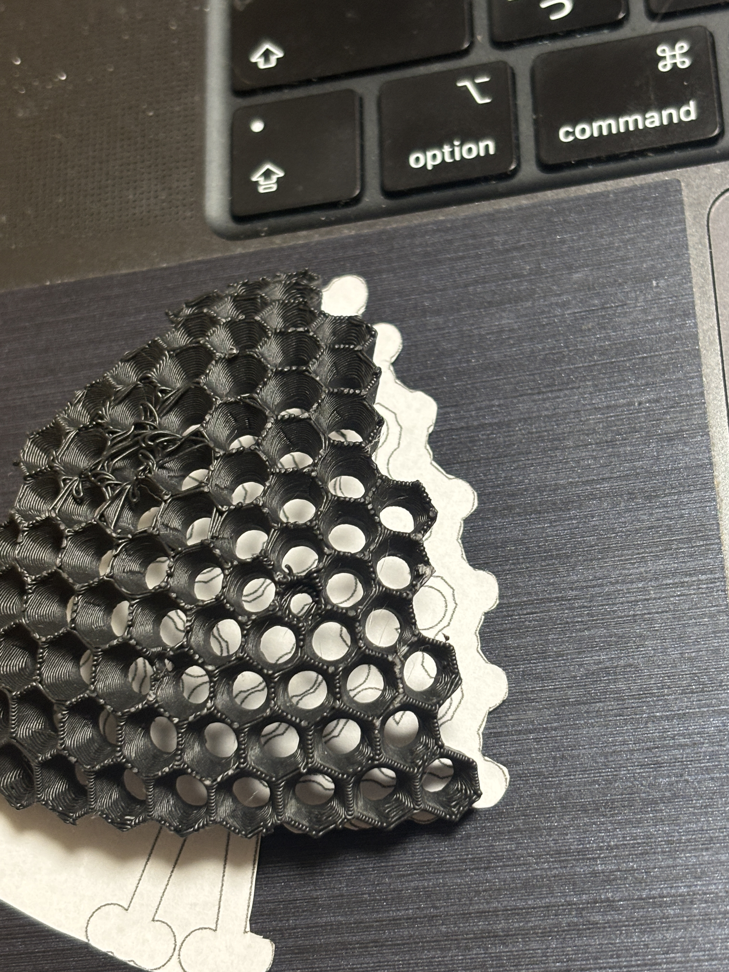
blog/images/avocado/IMG_8151.JPG
