sastles-com/FPC-isolation-sphere/blog/images/avocado/IMG_8153.JPG

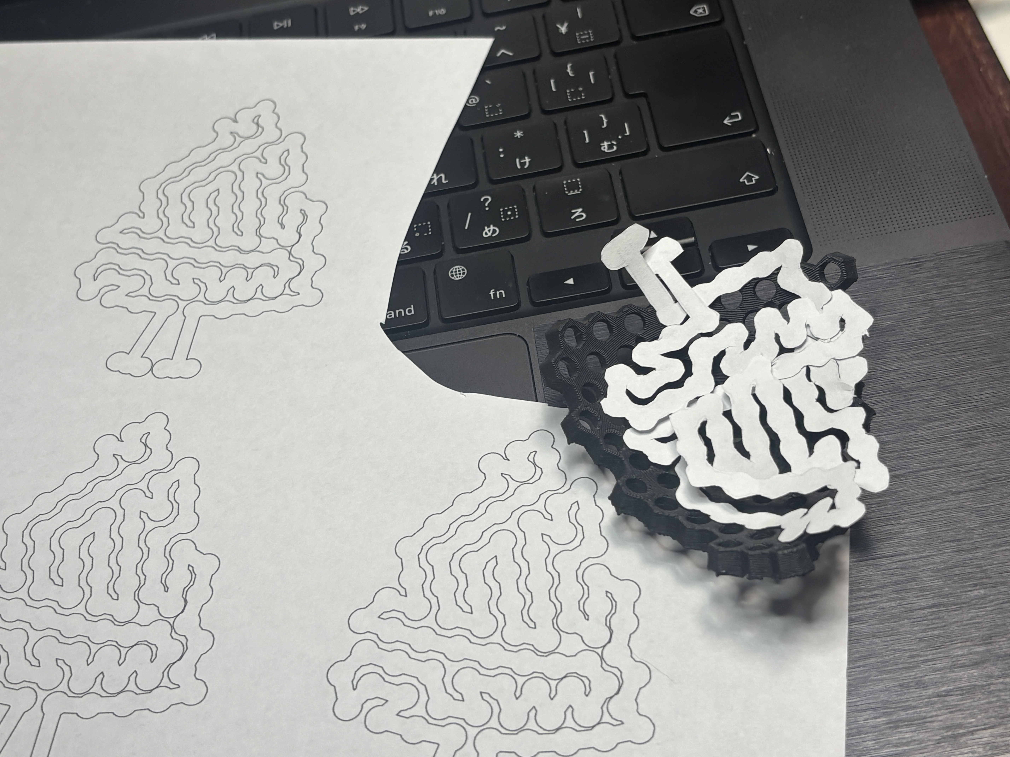
blog/images/avocado/IMG_8153.JPG
