sastles-com/FPC-isolation-sphere/blog/images/avocado/IMG_8154.JPG

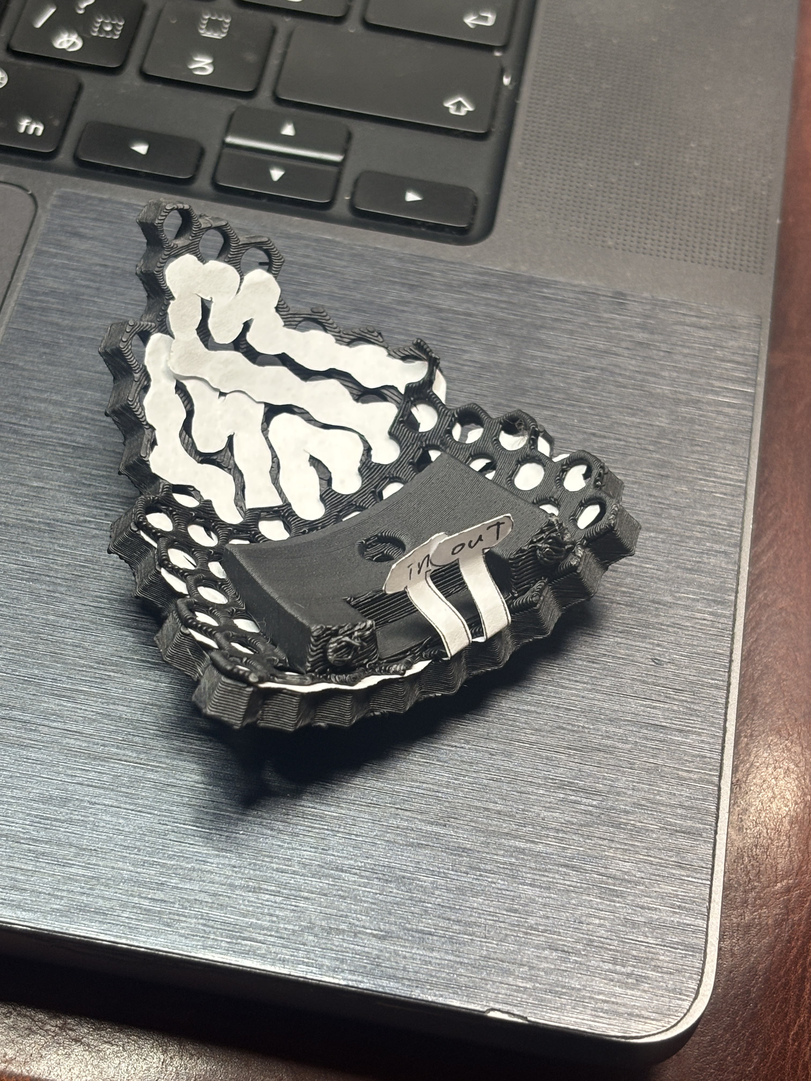
blog/images/avocado/IMG_8154.JPG
