sastles-com/FPC-isolation-sphere/blog/images/avocado/IMG_8158.JPG

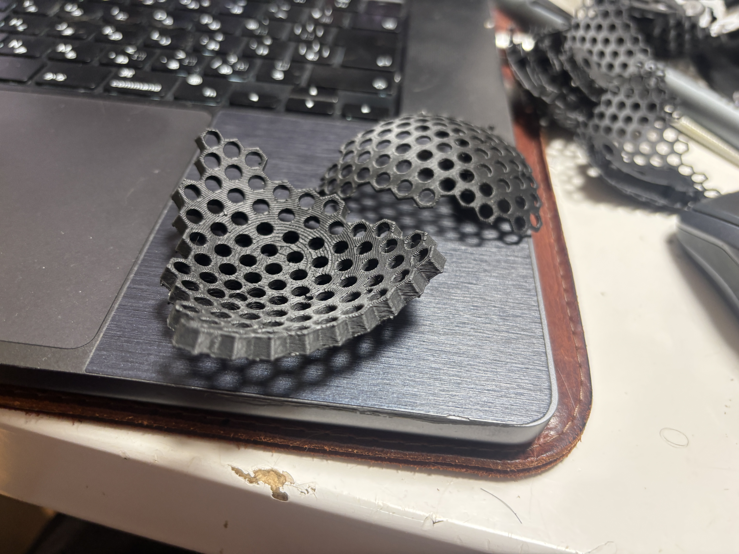
blog/images/avocado/IMG_8158.JPG
