sastles-com/FPC-isolation-sphere/blog/images/avocado/IMG_8162.JPG

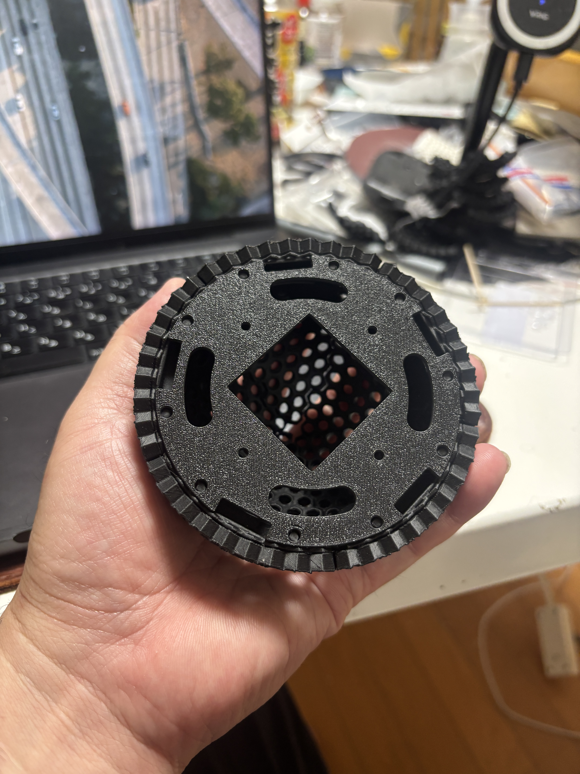
blog/images/avocado/IMG_8162.JPG
