sastles-com/FPC-isolation-sphere/blog/images/avocado/IMG_8163.JPG

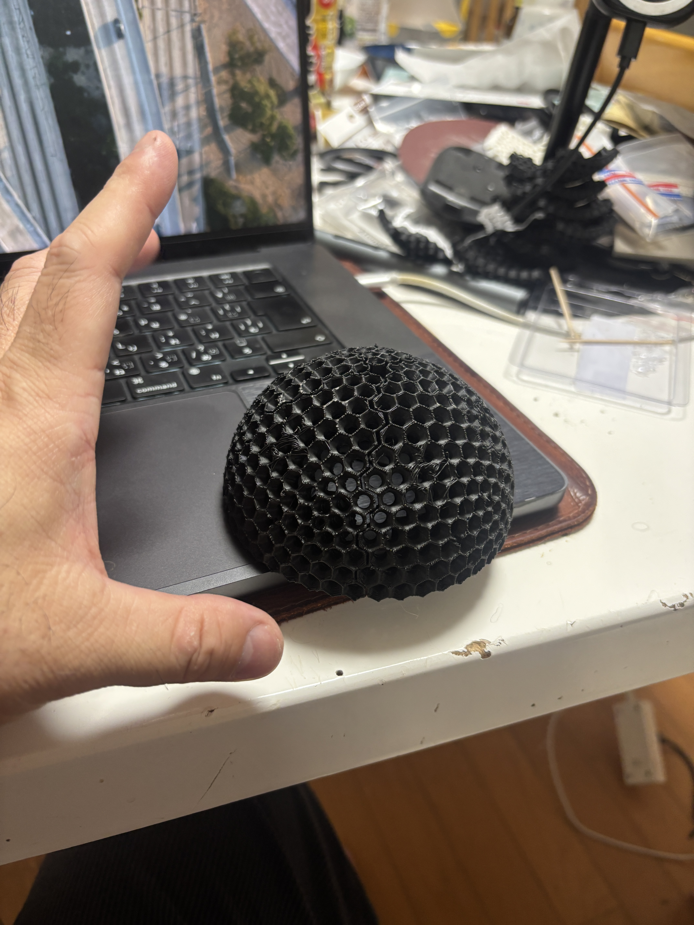
blog/images/avocado/IMG_8163.JPG
