sastles-com/FPC-isolation-sphere/blog/images/avocado/IMG_8187.JPG

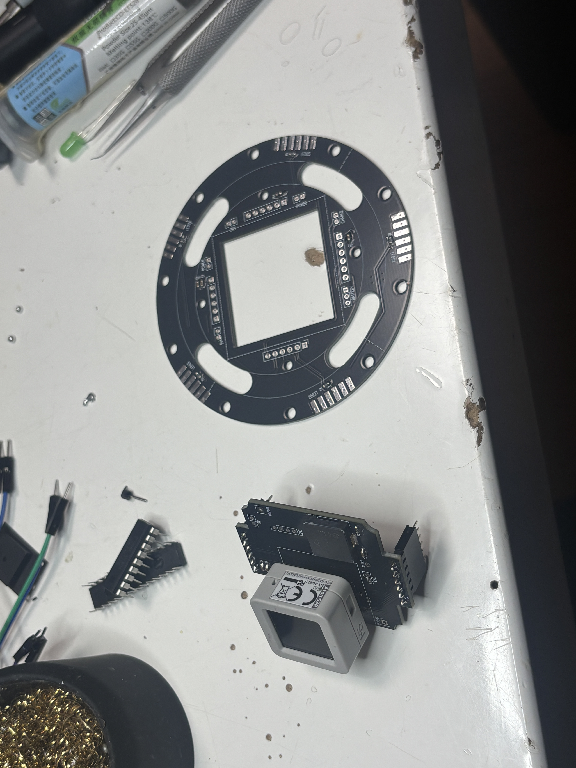
blog/images/avocado/IMG_8187.JPG
