sastles-com/FPC-isolation-sphere/blog/images/avocado/IMG_8189.JPG

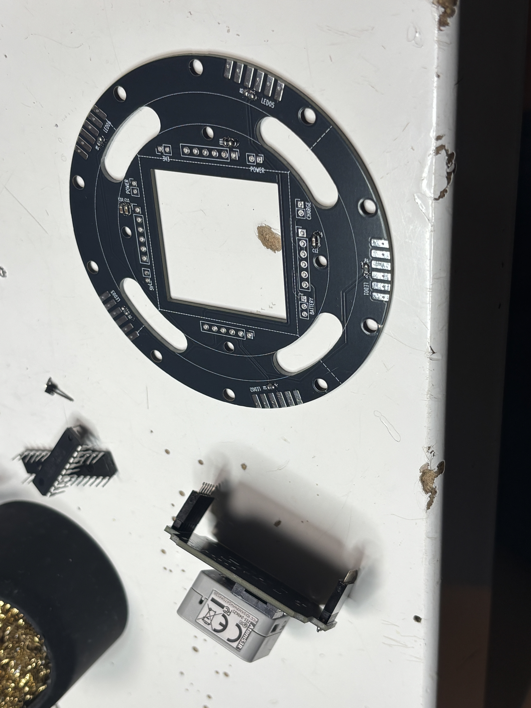
blog/images/avocado/IMG_8189.JPG
