sastles-com/FPC-isolation-sphere/blog/images/dodecahedron/IMG_7569.JPG

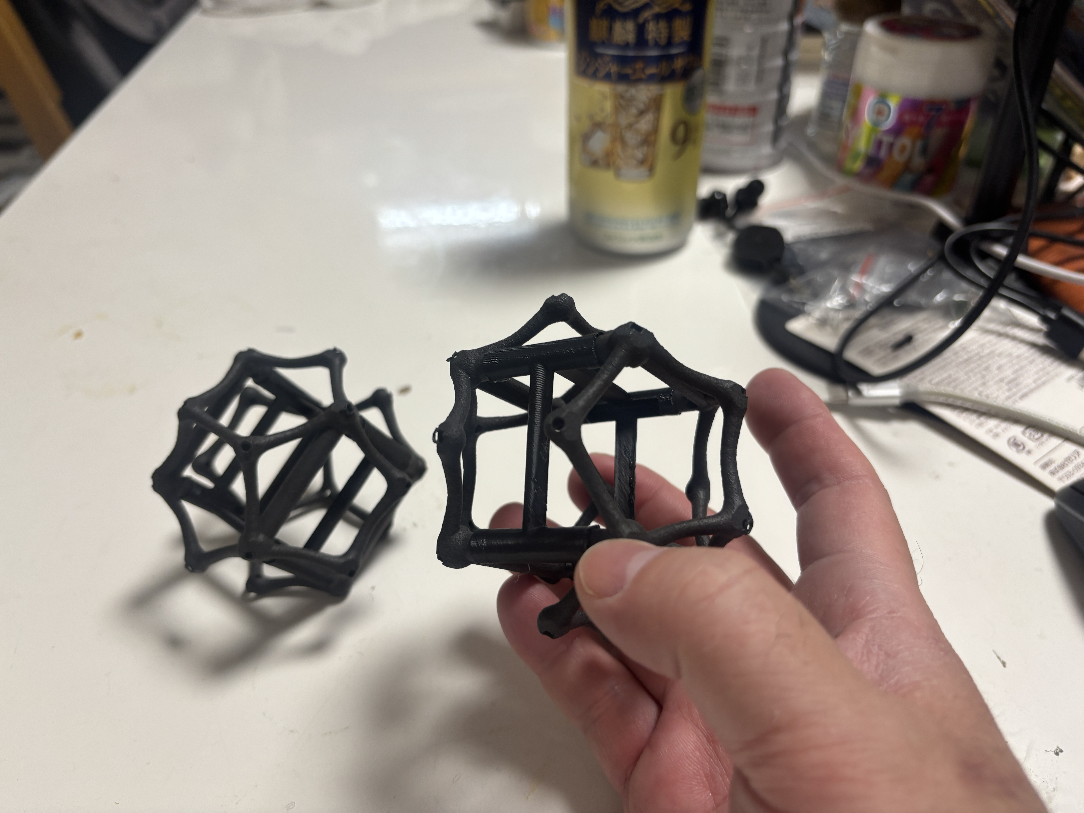
blog/images/dodecahedron/IMG_7569.JPG
