sastles-com/FPC-isolation-sphere/blog/images/dodecahedron/IMG_7803.JPG

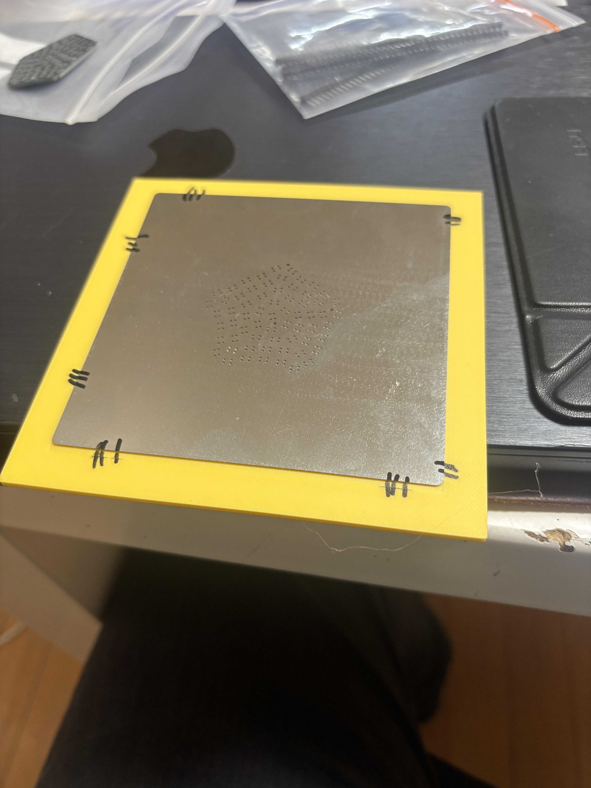
blog/images/dodecahedron/IMG_7803.JPG
