sastles-com/FPC-isolation-sphere/blog/images/dodecahedron/IMG_7804.JPG

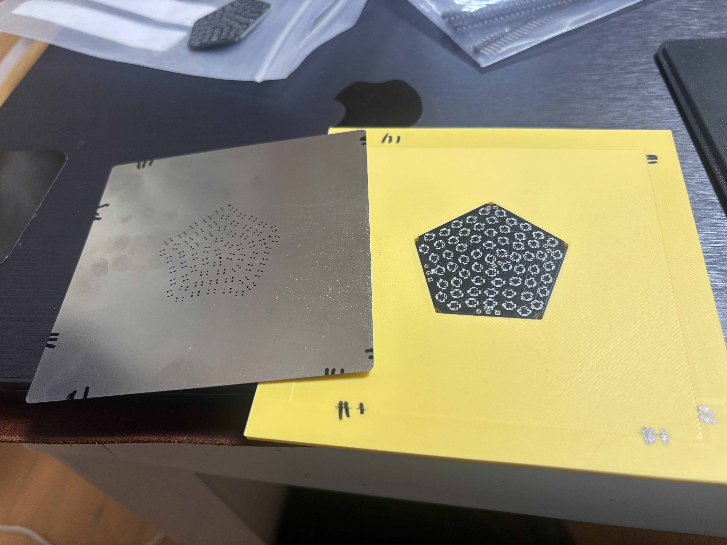
blog/images/dodecahedron/IMG_7804.JPG
