sastles-com/FPC-isolation-sphere/blog/images/dodecahedron/IMG_7806.JPG

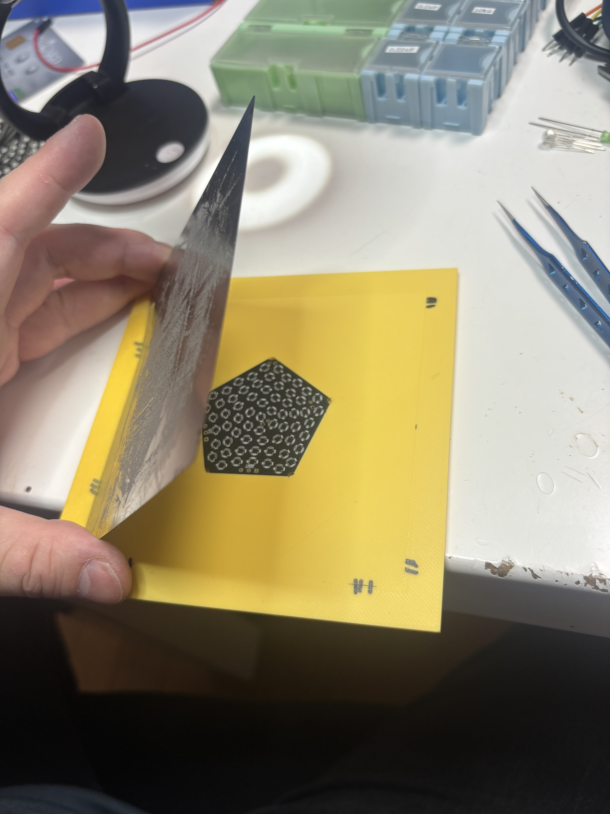
blog/images/dodecahedron/IMG_7806.JPG
