sastles-com/FPC-isolation-sphere/blog/images/dodecahedron/IMG_7807.JPG

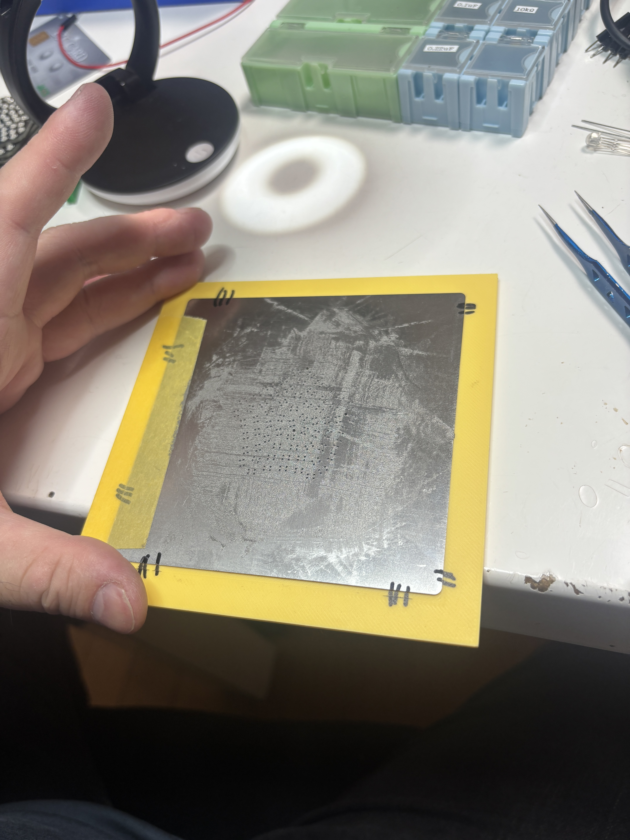
blog/images/dodecahedron/IMG_7807.JPG
