sastles-com/FPC-isolation-sphere/blog/images/dodecahedron/IMG_7808.JPG

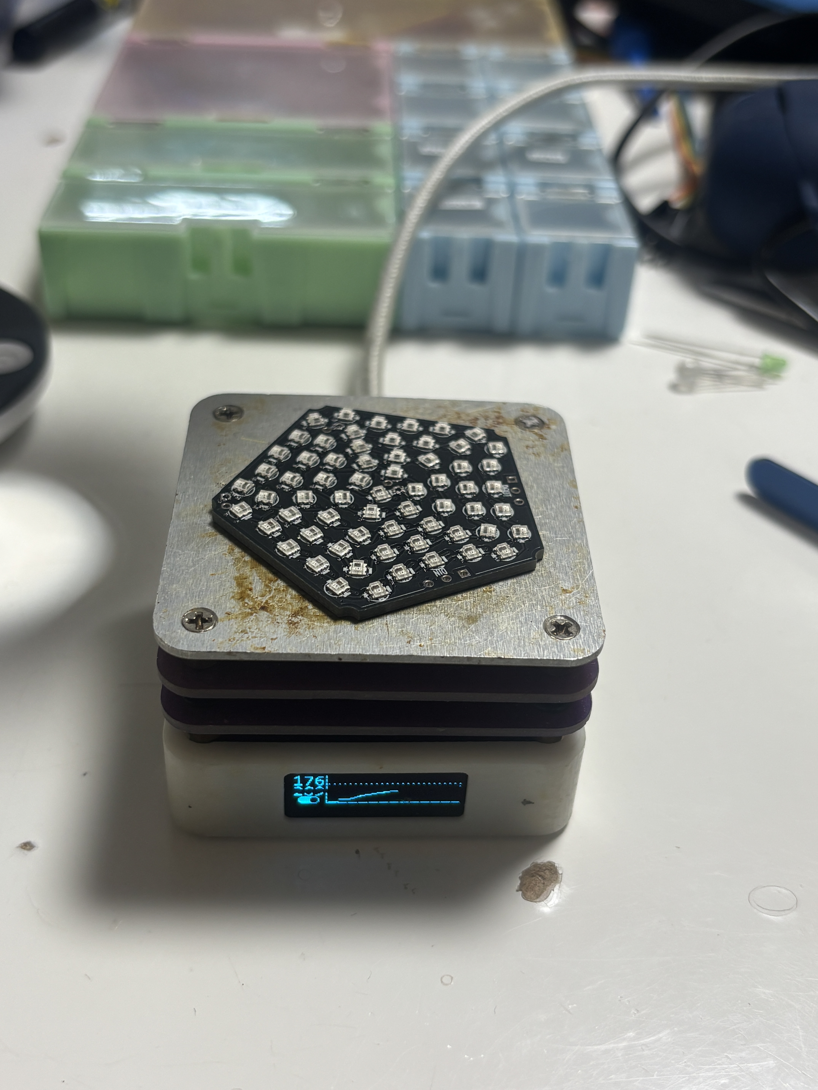
blog/images/dodecahedron/IMG_7808.JPG
