sastles-com/FPC-isolation-sphere/blog/images/dodecahedron/IMG_7809.JPG

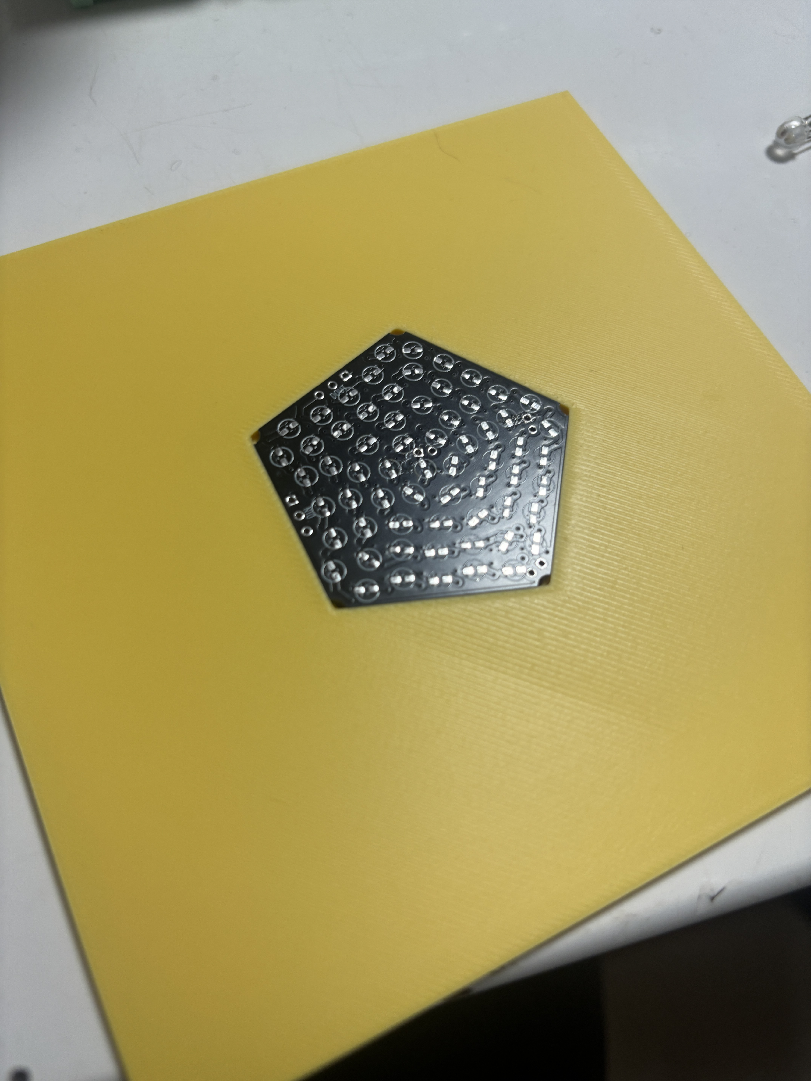
blog/images/dodecahedron/IMG_7809.JPG
