sastles-com/FPC-isolation-sphere/blog/images/dodecahedron/IMG_7810.JPG

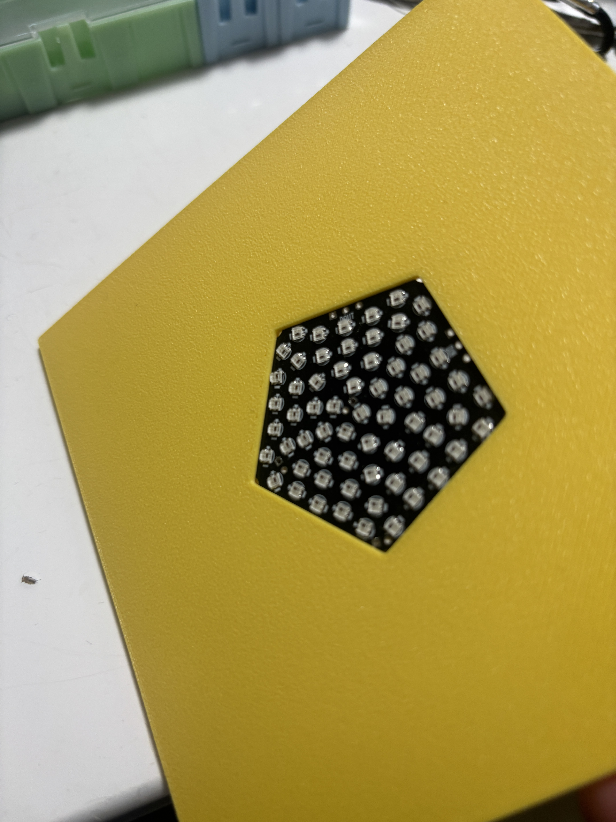
blog/images/dodecahedron/IMG_7810.JPG
