sastles-com/FPC-isolation-sphere/blog/images/dodecahedron/IMG_7811.JPG

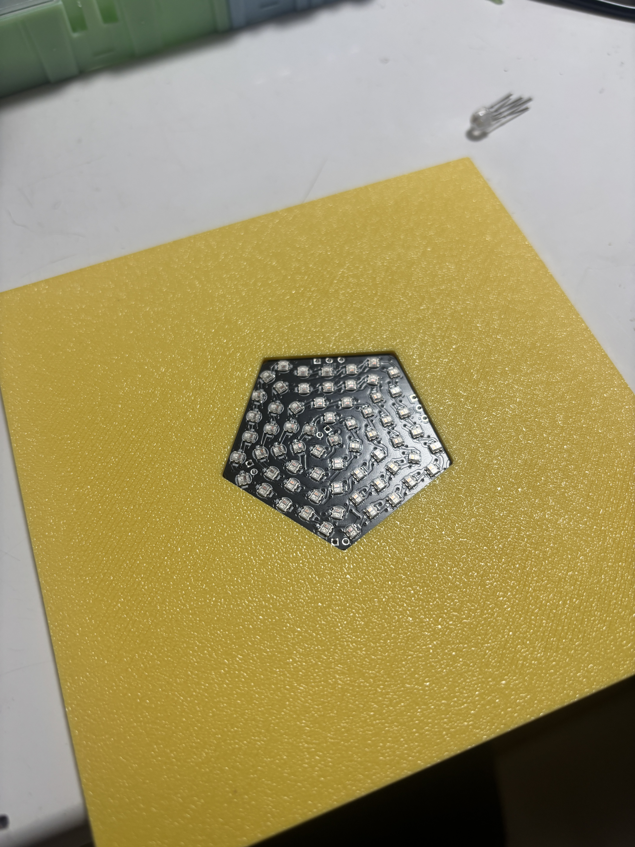
blog/images/dodecahedron/IMG_7811.JPG
