sastles-com/FPC-isolation-sphere/blog/images/dodecahedron/IMG_7877.JPG

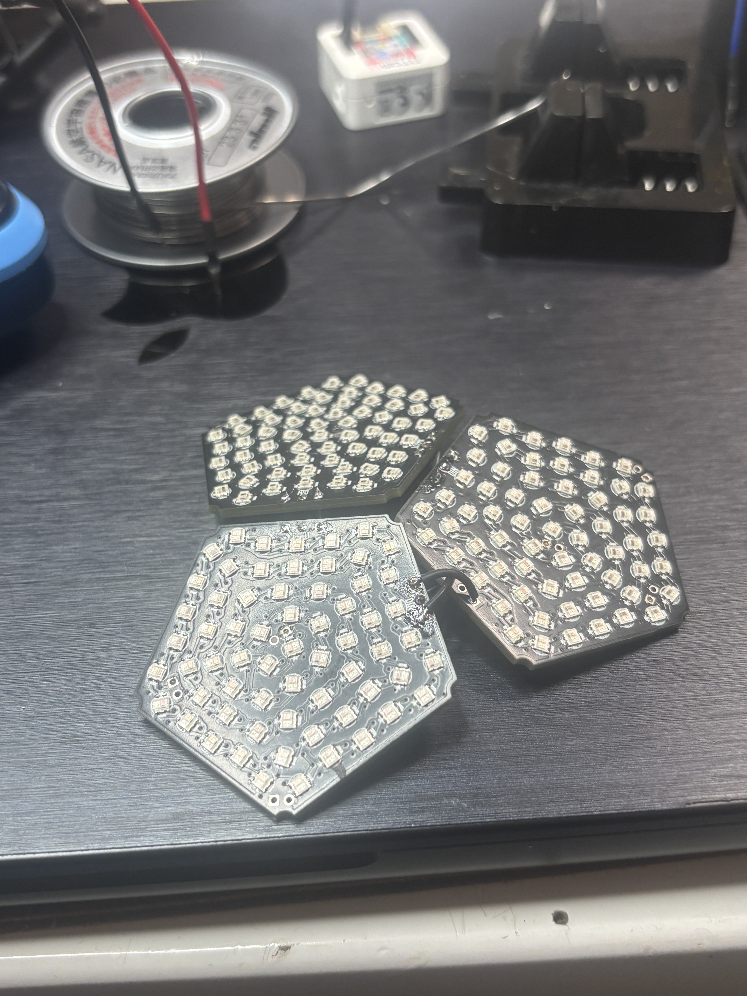
blog/images/dodecahedron/IMG_7877.JPG
