sastles-com/FPC-isolation-sphere/blog/images/dodecahedron/IMG_7878.JPG

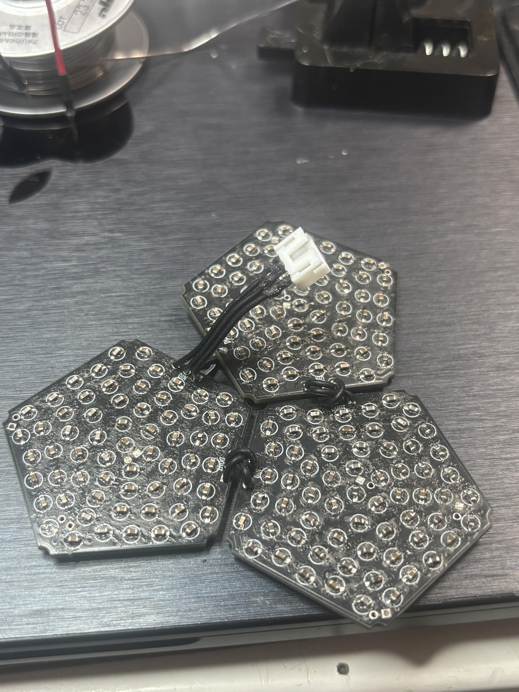
blog/images/dodecahedron/IMG_7878.JPG
