sastles-com/FPC-isolation-sphere/blog/images/dodecahedron/IMG_7882.JPG

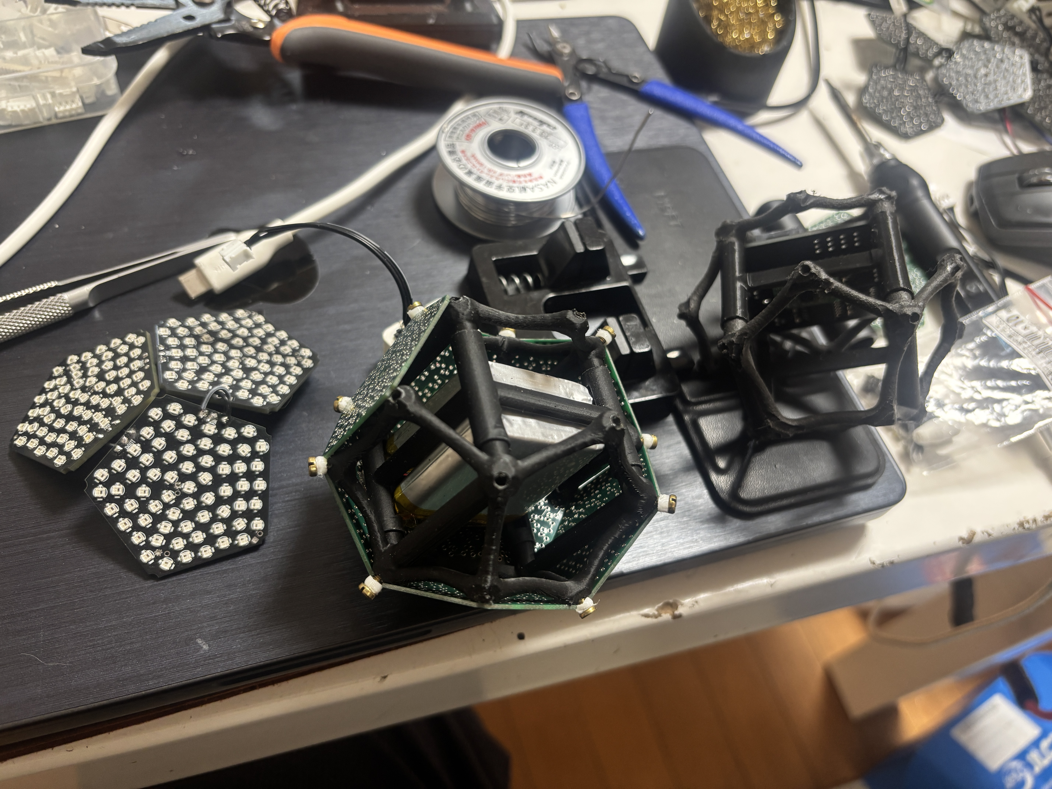
blog/images/dodecahedron/IMG_7882.JPG
