sastles-com/FPC-isolation-sphere/blog/images/dodecahedron/IMG_7883.JPG

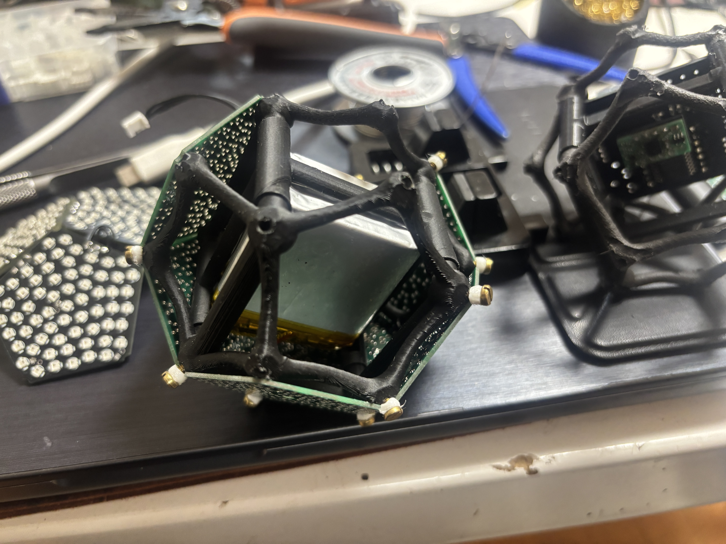
blog/images/dodecahedron/IMG_7883.JPG
