sastles-com/FPC-isolation-sphere/blog/images/dodecahedron/IMG_7884.JPG

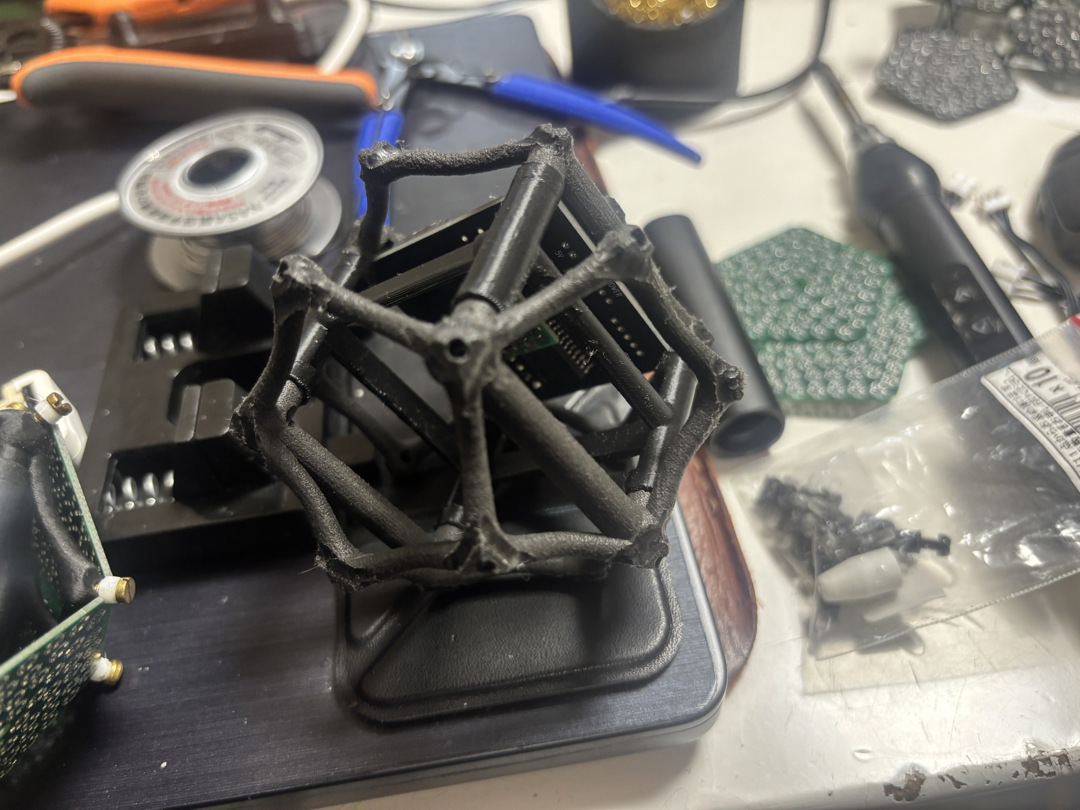
blog/images/dodecahedron/IMG_7884.JPG
