sastles-com/FPC-isolation-sphere/blog/images/dodecahedron/IMG_7885.JPG

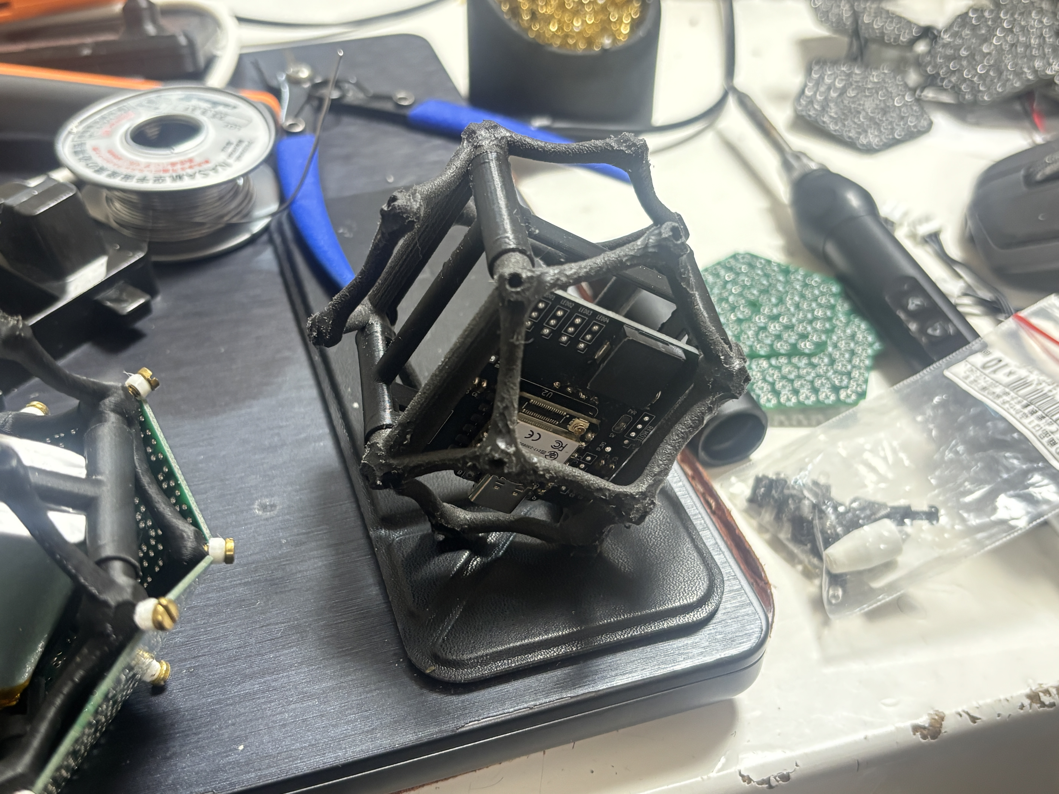
blog/images/dodecahedron/IMG_7885.JPG
