sastles-com/FPC-isolation-sphere/blog/images/dodecahedron/IMG_7969.JPG

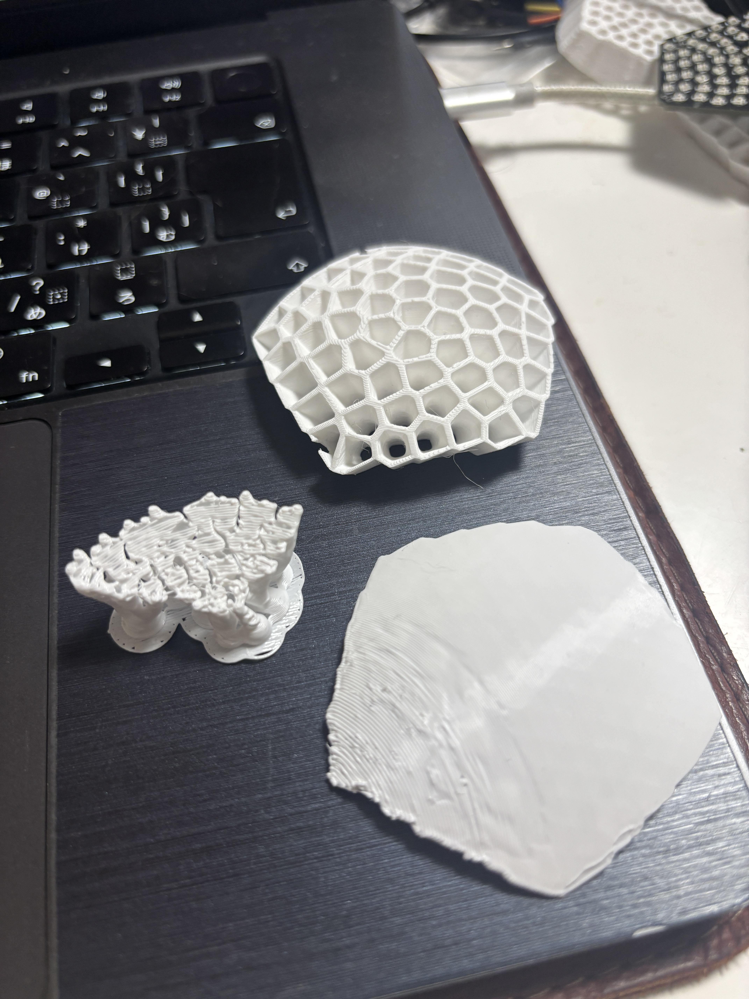
blog/images/dodecahedron/IMG_7969.JPG
