sastles-com/FPC-isolation-sphere/blog/images/dodecahedron/IMG_7971.JPG

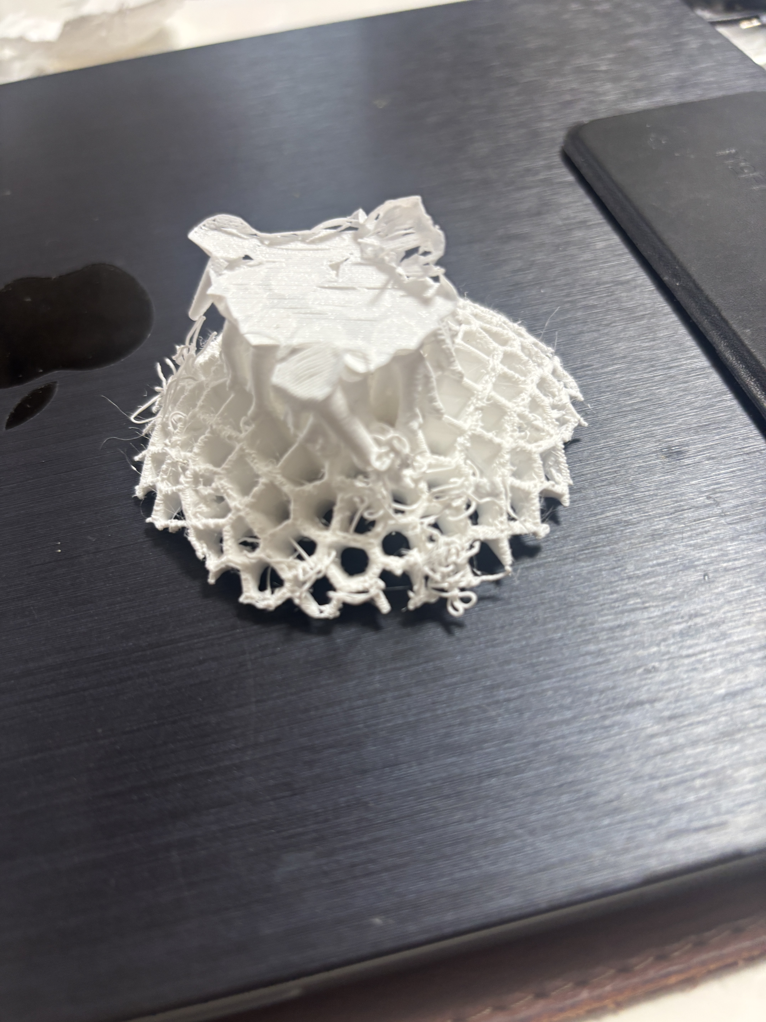
blog/images/dodecahedron/IMG_7971.JPG
