sastles-com/FPC-isolation-sphere/blog/images/dodecahedron/IMG_7973.JPG

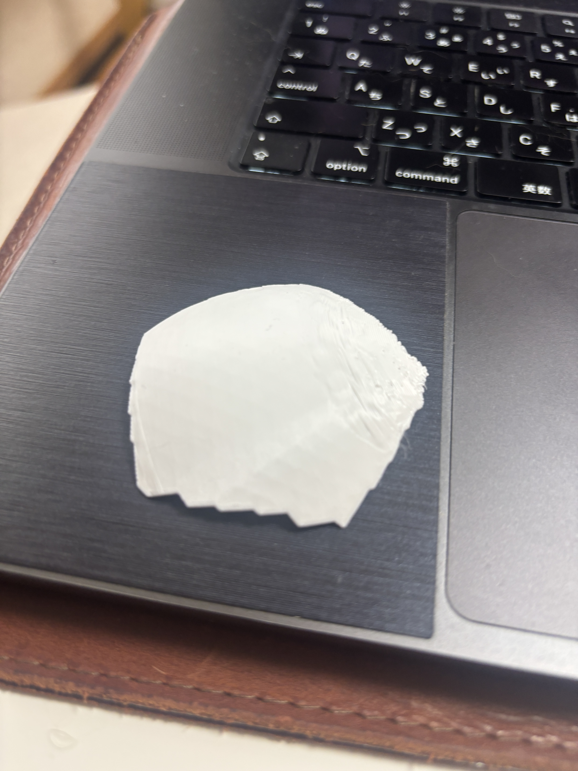
blog/images/dodecahedron/IMG_7973.JPG
