sastles-com/FPC-isolation-sphere/blog/images/dodecahedron/IMG_7978.JPG

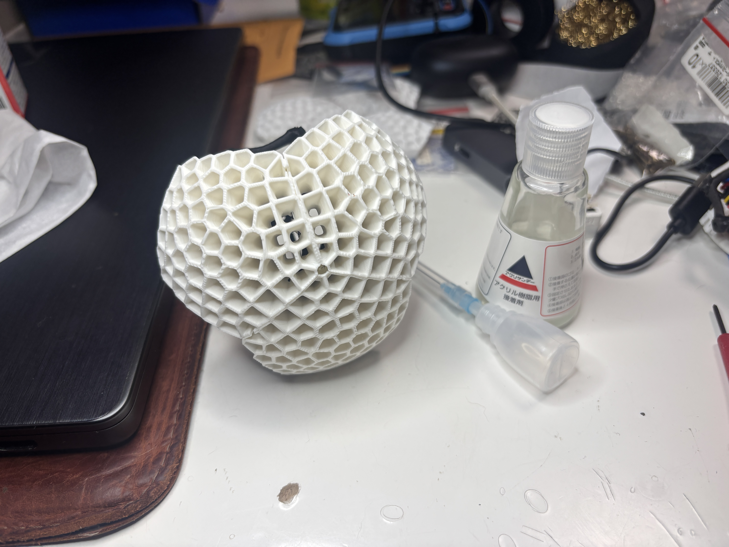
blog/images/dodecahedron/IMG_7978.JPG
