sastles-com/FPC-isolation-sphere/blog/images/dodecahedron/IMG_7979.JPG

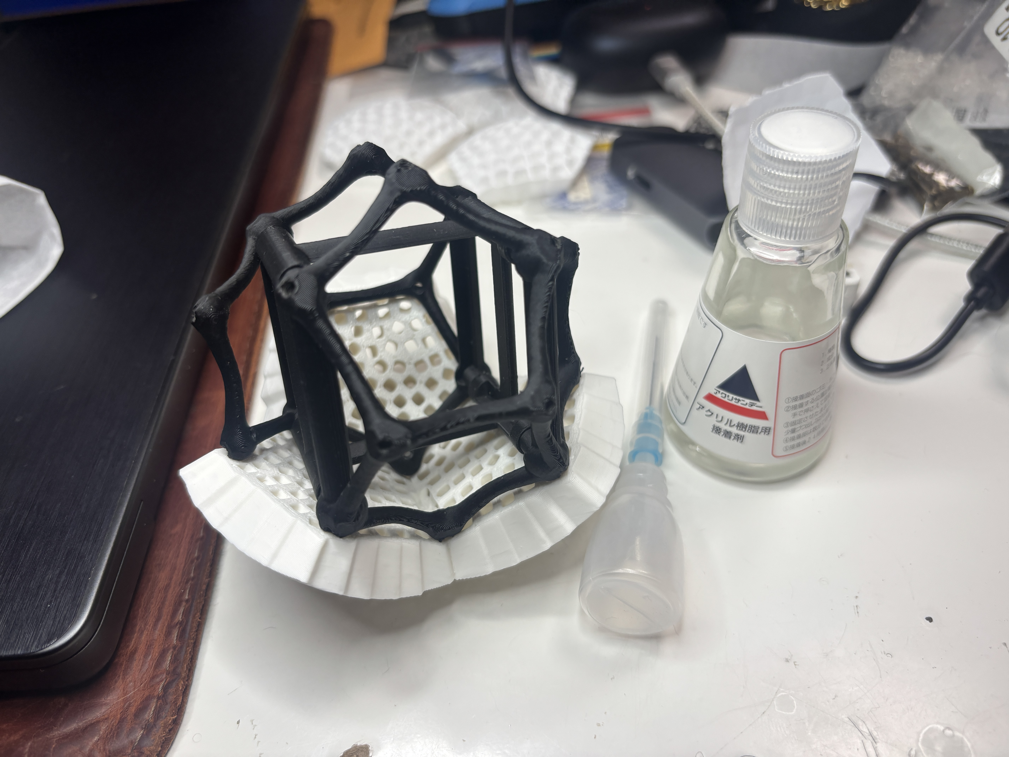
blog/images/dodecahedron/IMG_7979.JPG
