sastles-com/FPC-isolation-sphere/blog/images/dodecahedron/IMG_7980.JPG

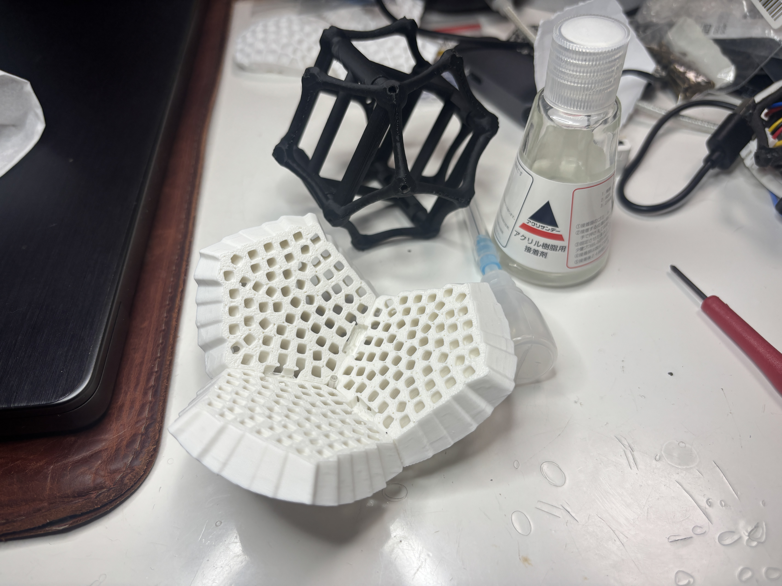
blog/images/dodecahedron/IMG_7980.JPG
