sastles-com/FPC-isolation-sphere/blog/images/dodecahedron/IMG_7986.JPG

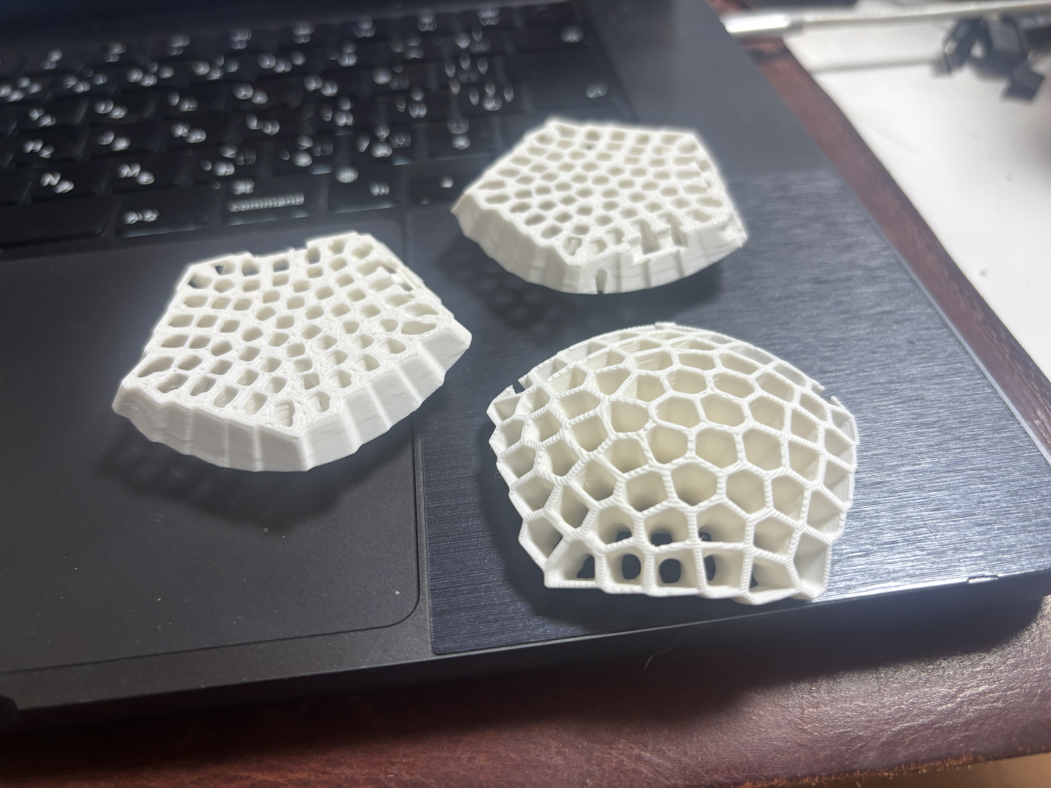
blog/images/dodecahedron/IMG_7986.JPG
