sastles-com/FPC-isolation-sphere/blog/images/dodecahedron/IMG_8015.JPG

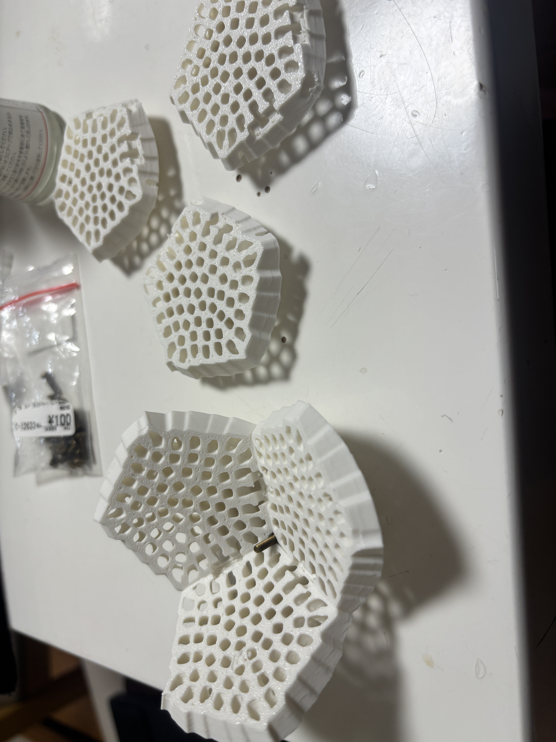
blog/images/dodecahedron/IMG_8015.JPG
