sastles-com/FPC-isolation-sphere/blog/images/dodecahedron/IMG_8017.JPG

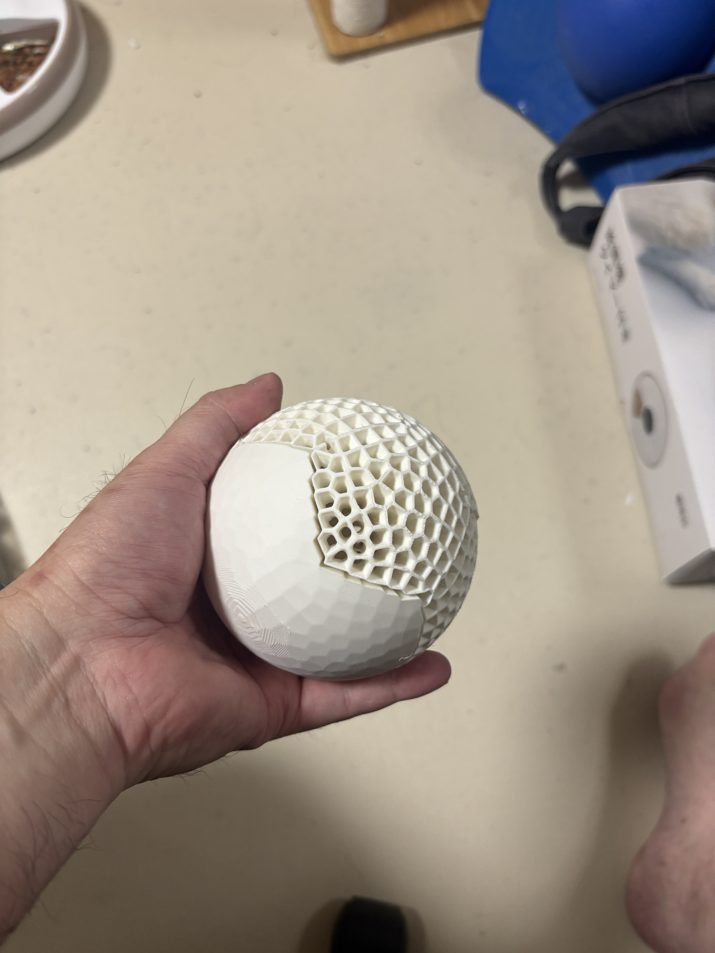
blog/images/dodecahedron/IMG_8017.JPG
