sastles-com/FPC-isolation-sphere/blog/images/dodecahedron/IMG_8019.JPG

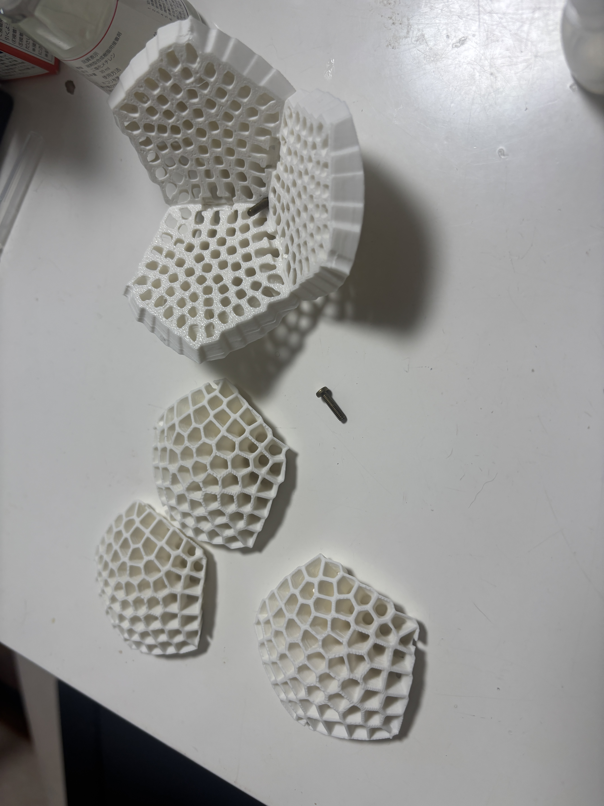
blog/images/dodecahedron/IMG_8019.JPG
