sastles-com/FPC-isolation-sphere/blog/images/dodecahedron/IMG_8034.JPG

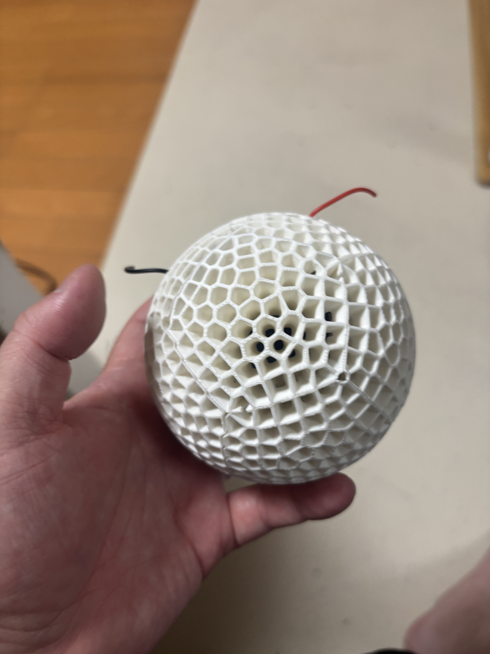
blog/images/dodecahedron/IMG_8034.JPG
