sastles-com/FPC-isolation-sphere/blog/images/dodecahedron/IMG_8035.JPG

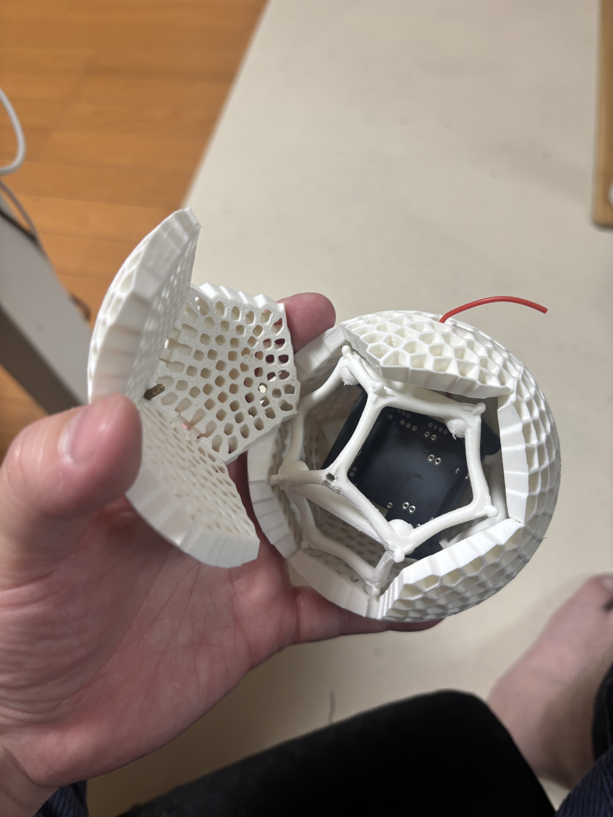
blog/images/dodecahedron/IMG_8035.JPG
