sastles-com/FPC-isolation-sphere/blog/images/dodecahedron/IMG_8036.JPG

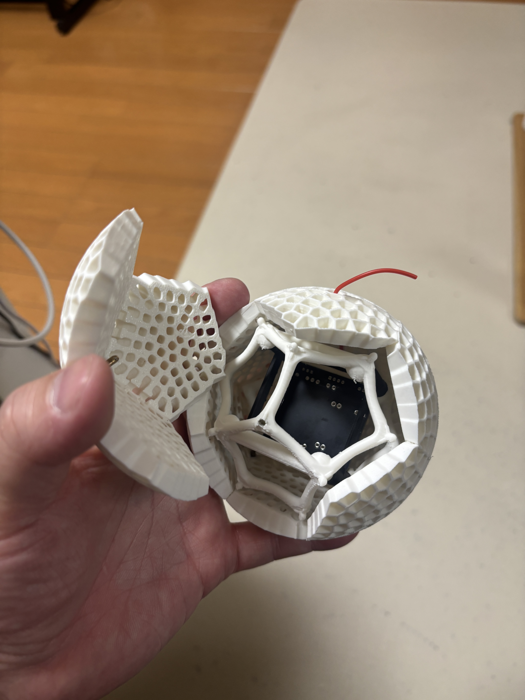
blog/images/dodecahedron/IMG_8036.JPG
