sastles-com/FPC-isolation-sphere/blog/images/dodecahedron/IMG_8037.JPG

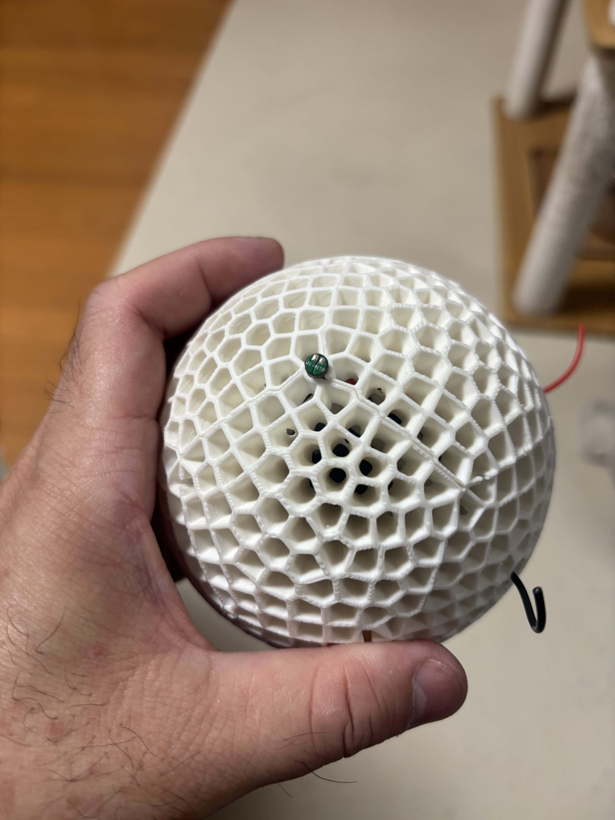
blog/images/dodecahedron/IMG_8037.JPG
