sastles-com/FPC-isolation-sphere/blog/images/dodecahedron/IMG_8038.JPG

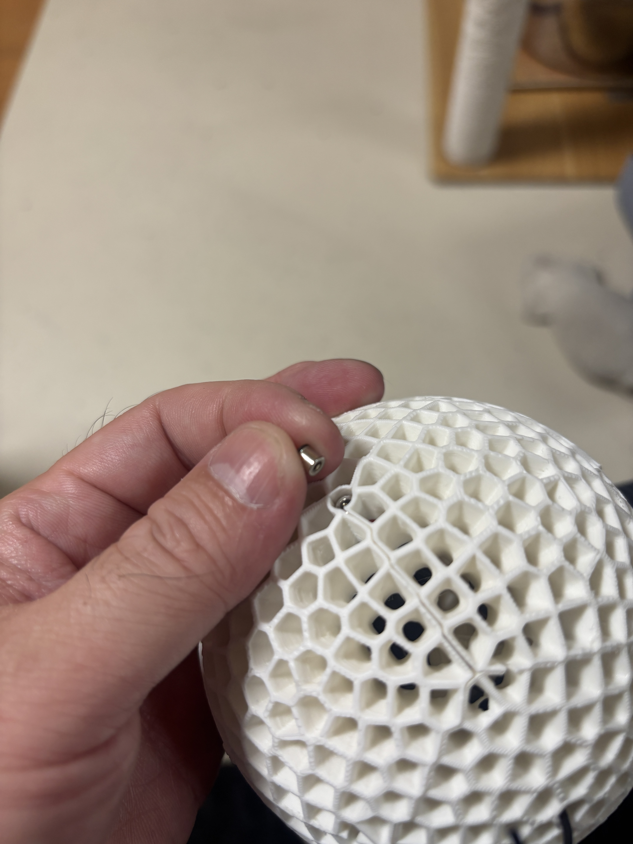
blog/images/dodecahedron/IMG_8038.JPG
