sastles-com/FPC-isolation-sphere/blog/images/dodecahedron/IMG_8119.JPG

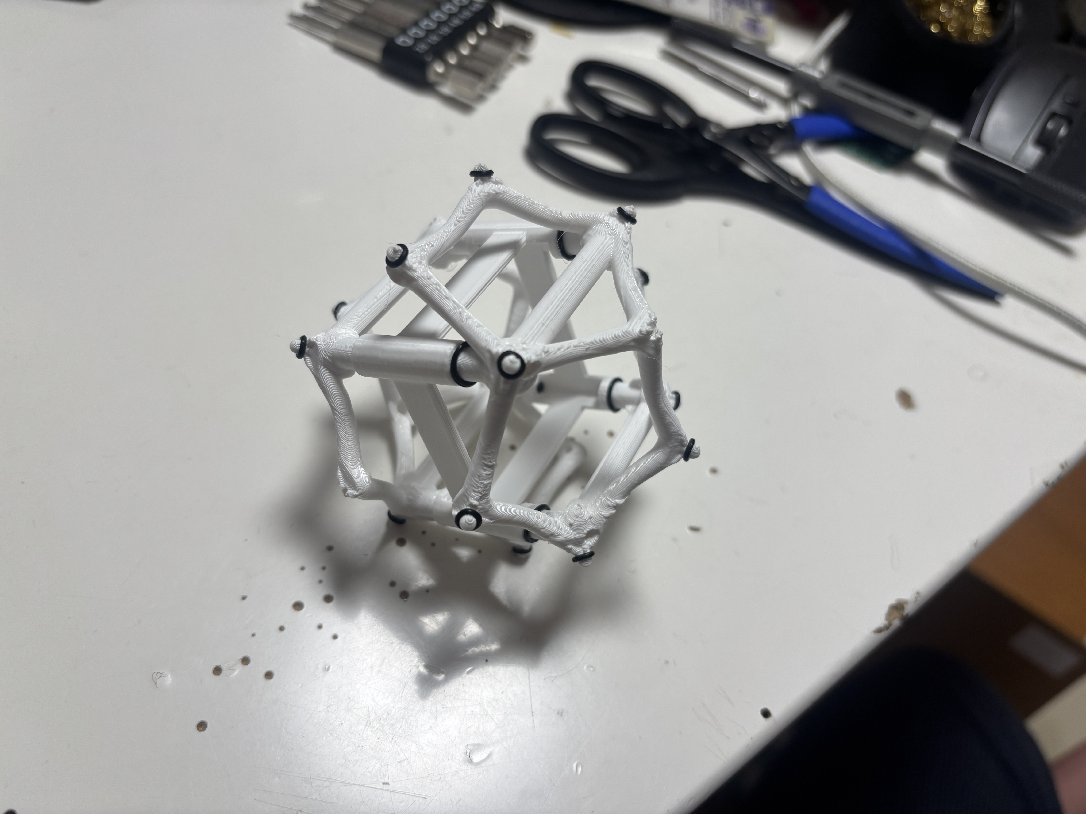
blog/images/dodecahedron/IMG_8119.JPG
