sastles-com/FPC-isolation-sphere/blog/images/dodecahedron/IMG_8120.JPG

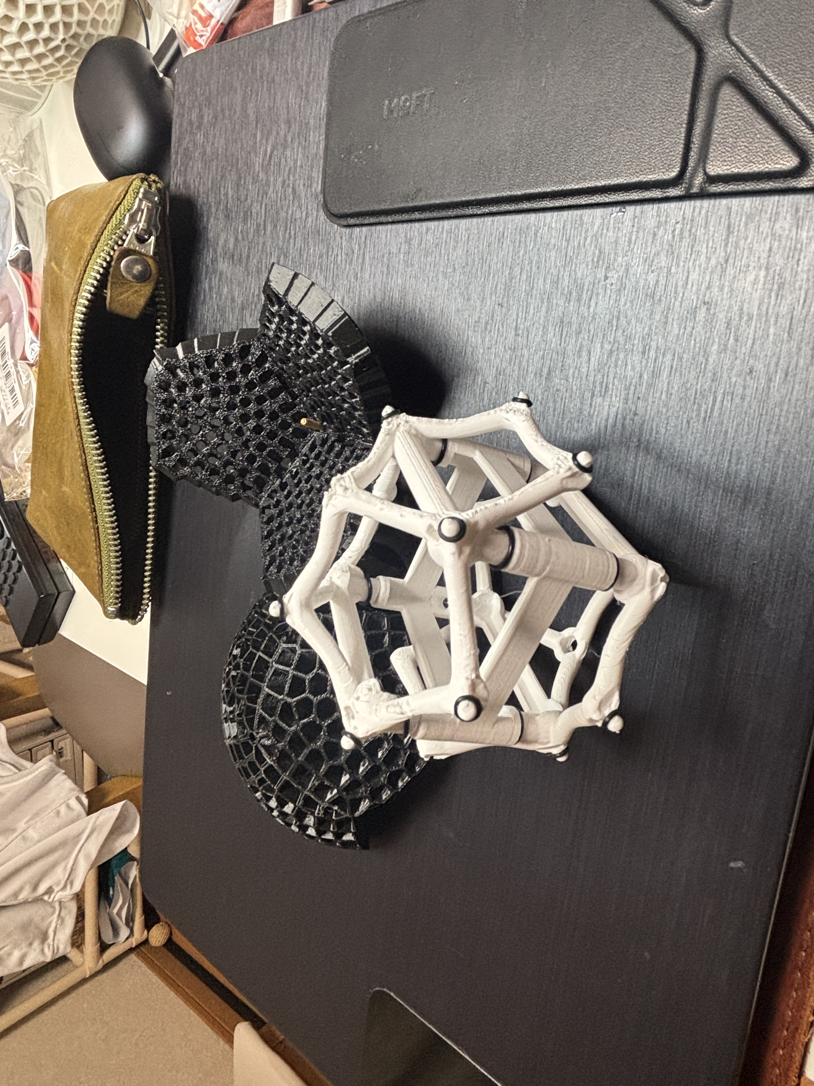
blog/images/dodecahedron/IMG_8120.JPG
