sastles-com/FPC-isolation-sphere/blog/images/dodecahedron/IMG_8126.JPG

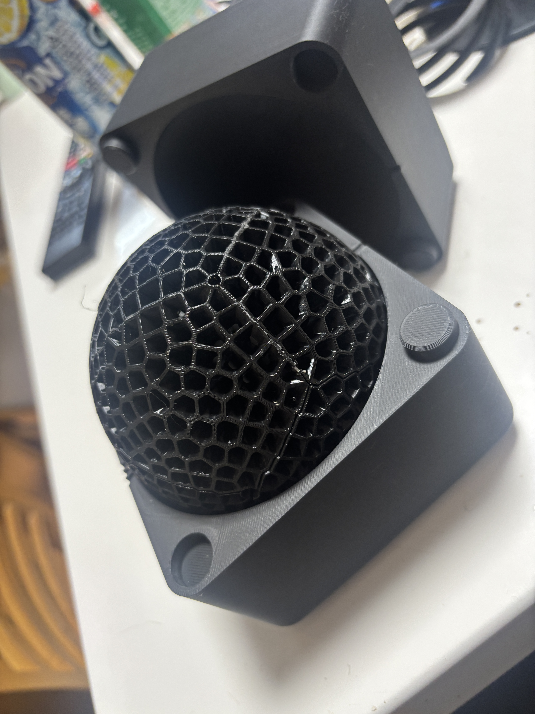
blog/images/dodecahedron/IMG_8126.JPG
