sastles-com/FPC-isolation-sphere/blog/images/dodecahedron/IMG_8127.JPG

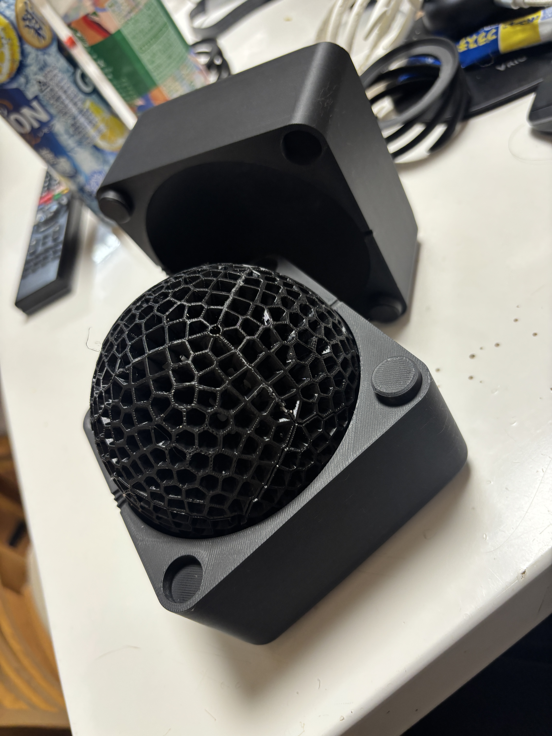
blog/images/dodecahedron/IMG_8127.JPG
