sastles-com/FPC-isolation-sphere/blog/images/dodecahedron/IMG_8128.JPG

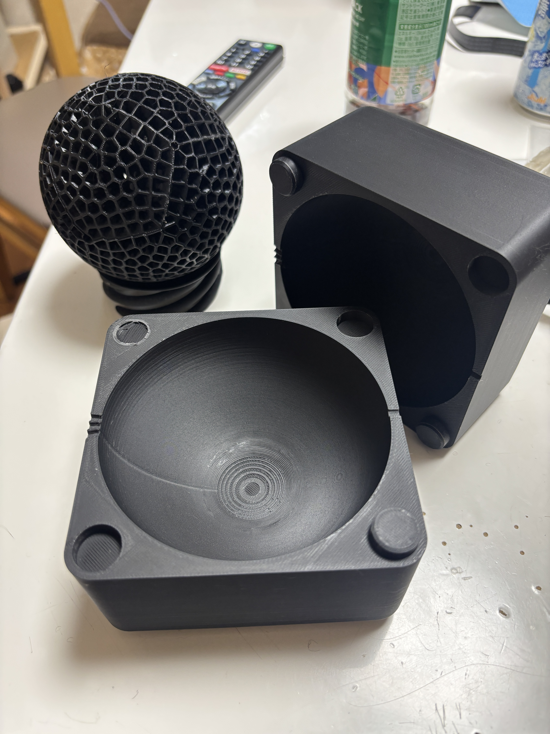
blog/images/dodecahedron/IMG_8128.JPG
